OpenDevicePartnership/pico-de-gallo/docs/superpowers/specs/2026-08-19-zephyr-mfd-m5-acceptance.md

# Zephyr MFD restructure M5 — loopback integration and hardware acceptance

Date: 2026-08-19
Branch: `zephyr`, baseline `cfb7f4245ed3`
Milestone: M5 — runtime verification after standard `cs-gpios`
Related implementation: `0affe9206553`
Status: amended after architecture and reliability review

---

## 1. Context, scope and stop conditions

M1–M4 established the MFD topology, GPIO child and standard SPI `cs-gpios`, but
runtime behaviour remains largely unproved. M5 must independently establish:

1. the physical fixture is valid;
2. chip select asserts, holds and releases through GPIO 2↔3;
3. synchronous SPI data is bit-exact on the MOSI↔MISO short;
4. the sanctioned payload ceiling fails locally rather than at transport; and
5. the checked-deassert failure and process-local latch behave as specified.

The fixture is board `5256657D8A5D7F03`, hardware revision 2, attached to WSL by
usbipd. Windows cannot access it while attached. Every build and run is inside
WSL. One process may own USB and one build may run at a time.

### 1.1 Hard boundaries

- Nothing under `crates/`; no wire, firmware, version or lockfile change.
- No firmware flashing, `probe-rs`, GPIO interrupts, or `gallo_*` MCP call.
- No production-driver edit except `PDG_SPI_MAX_BUFFER` and its adjacent comment.
- Test applications may call existing C FFI entry points directly. They may not
  add, alter or emulate an FFI entry point.
- Any other driver defect is stop-and-report, never a silent repair or weakened
  expectation.
- Every hardware process is wall-clock bounded. Timeout is **infrastructure
  failure**, never a test result.
- Any abnormal hardware phase restarts through §9.4. Later phases never consume
  residue from an abnormal predecessor.

---

## 2. Architecture and complete file set

Normal acceptance is serialized:

```text
reset_subscriptions -> jumper_preflight -> acceptance -> spi_loopback -> recovery_teardown
```

The images share only the parent-identity DTS fragment. Their topology overlays
are deliberately different. A phase advances only after zero exit, its exact
success marker, and verified USB release.

### 2.1 Authorized M5 files

| Action | Path | Responsibility |
| --- | --- | --- |
| Create | `docs/superpowers/specs/2026-08-19-zephyr-mfd-m5-acceptance.md` | This specification. |
| Create | `zephyr/tests/pdg_mfd_m5/fixture-identity.dtsi` | Explicit lab-fixture serial only. |
| Create | `zephyr/tests/pdg_mfd_m5/common/m5_bottom.{h,c}` | Host-context shim: `reset_subscriptions`, `gpio_subscribe`, `gpio_unsubscribe`, `spi_get_config`. |
| Create | `zephyr/tests/pdg_mfd_m5/reset_subscriptions/{CMakeLists.txt,prj.conf,reset.overlay,src/main.c}` | Parent-only reset image. |
| Create | `zephyr/tests/pdg_mfd_m5/jumper_preflight/{CMakeLists.txt,prj.conf,jumper.overlay,src/main.c}` | Parent+GPIO image; SPI disabled. |
| Create | `zephyr/tests/pdg_mfd_m5/acceptance/{CMakeLists.txt,prj.conf,acceptance.overlay,src/main.c}` | Parent+GPIO+SPI behavioural acceptance, including a payload-before-only execution mode. |
| Create | `zephyr/tests/pdg_mfd_m5/recovery_teardown/{CMakeLists.txt,prj.conf,recovery.overlay,src/main.c}` | Parent+GPIO+SPI recovery and final-state report. |
| Create | `zephyr/tests/pdg_mfd_m5/run-m5.sh` | Serialized probes, bounded runners, restart handling and aggregate verdict. |
| Create | `zephyr/tests/pdg_mfd_m5/spi_loopback.overlay` | Upstream slow/fast children and CS 2. |
| Create | `zephyr/tests/pdg_mfd_m5/spi_loopback.conf` | Async off, 512-byte large buffer, measured latency scale. |
| Modify | `zephyr/drivers/spi/pdg_spi.c` | Constant and adjacent comment only. |
| Modify | `zephyr/drivers/spi/Kconfig` | Keep the additive heap default at 8192; correct the help text to the final ceiling plus allocator metadata/alignment margin. |
| Modify | `zephyr/dts/bindings/spi/odp,pico-de-gallo-spi.yaml` | Both SPI ceiling statements. |
| Modify | `zephyr/README.md` | SPI ceiling row at current line 582. |
| Modify | `book/src/interfaces/spi.md` | Zephyr SPI error ceiling at current lines 212–214. |
| Modify | `zephyr/CHANGELOG.md` | Corrected ceiling and M5 acceptance evidence. |

Grep found other `4096` references in `book/`, but they describe the FFI,
batching, firmware buffers, or generic firmware APIs and remain valid. The I2C
constant and `zephyr/README.md:564` are also unchanged. Same-change parity for
the six Zephyr SPI files above is mandatory; M6 deferral is prohibited.

**Amendment (coordinator, during implementation): `common/m5_bottom.{h,c}`.**
`native_sim` splits into an embedded context (the applications' `src/main.c`) and
a host context (the native simulator runner). `pico_de_gallo.h` is on the host
include path only — `zephyr/CMakeLists.txt` adds it through
`target_compile_options(native_simulator INTERFACE "-I…")` — which is precisely
why every production driver has a `pdg_*_bottom.c`. An embedded translation unit
therefore cannot call `gallo_*` directly, so §1.1's "test applications may call
existing C FFI entry points directly" is unimplementable as written for the four
entry points that have no production bottom half: `gallo_system_reset_subscriptions`
(§3, §10 step 1), `gallo_gpio_subscribe` and `gallo_gpio_unsubscribe` (§6.2 steps
2, 5 and 9), and `gallo_spi_get_config` (§10 step 4). `gallo_gpio_set_config`
(§6.2 step 6) is unaffected: `pdg_gpio_bottom_set_config()` already exposes it.
The shim is wired per-application with `target_sources(native_simulator INTERFACE
…)`, the same mechanism `zephyr/drivers/CMakeLists.txt` already uses; it adds no
FFI entry point, alters none, emulates none, and modifies no production driver.

**Amendment (coordinator): tester escalation E2 needs no value change.**
`CONFIG_HEAP_MEM_POOL_ADD_SIZE_PDG_SPI` in `zephyr/drivers/spi/Kconfig` already
defaults to **8192**, not the 6144 E2 assumed; E2 read the upstream test's
default rather than this module's. The driver's two `k_malloc`s (`pdg_spi.c:457`,
`:464`) leave roughly 1.9 KiB for `sys_heap` metadata, the heap header and
alignment. Only the Kconfig **help text** is wrong — it still says "4096" and
"about 8 KiB" — and that is a §4 documentation-parity fix, not a configuration
change. Do not "fix" the value a second time.

### 2.2 Topology contracts

- **Reset:** parent `okay`; GPIO and SPI explicitly `disabled`.
- **Jumper:** parent and GPIO `okay`; SPI explicitly `disabled`.
- **Acceptance/recovery:** parent, GPIO and SPI `okay`; CS index 2.
- **Loopback:** same controllers plus `slow@0` and `fast@0` at selector 0.

Each build must assert generated devicetree status, not infer topology from
translation units. In particular, reset must prove both children disabled before
its executable may run.

### 2.3 Fixture identity policy

Commit serial `5256657D8A5D7F03`. It is lab-fixture metadata, not a credential.
Because `zephyr/module.yml:11-12` exports `zephyr/tests`, it **ships in clones and
source archives**. It is intentionally excluded only from portable samples,
which retain `REPLACE_WITH_YOUR_PICO_DE_GALLO_SERIAL`. The identity fragment must
say in a comment: “M5 lab fixture only; do not copy this serial into user
overlays.”

### 2.4 No interrupt witness

Do not set `cs-loopback-gpios`. Current upstream `spi.c:140` guards the complete
witness implementation; omission selects no-op helpers at 242–246. Defining it
reaches interrupt configuration at 233 and callback registration at 240. No other
file under the suite's `src/` uses GPIO interrupts.

---

## 3. Reset sequencing and endpoint limits

The reset image is the resolution of the init-order conflict. Parent init performs
strict open before `main()` directly calls
`gallo_system_reset_subscriptions(ctx, &count)`. GPIO/SPI are absent, so monitored
pin 2 cannot fail SPI init first.

Required reset behaviour:

1. require parent readiness and a non-NULL borrowed context;
2. call reset exactly once and compare its return against the symbolic success
   enumerator from the **actual generated cbindgen header**;
3. print reset count and `M5_RESET_PASS` only after success;
4. any failed check terminates nonzero.

Do not write `Status_Ok`, `GalloStatus_Ok`, bare `0`, or another guessed spelling
in the specification-derived implementation. Inspect the generated header during
the build and use its symbolic enumerator. Current cbindgen configuration keeps
`Status` variants unprefixed and `common.c:19` uses `Ok`, but the generated header
is authoritative.

“Idempotent” is conditional: reset is safe when the firmware dispatcher can
service the endpoint. It cannot preempt an outstanding serial, zero-timeout
`gpio/wait-*`; such a wait wedges dispatch device-wide. Reset affects
**subscriptions only**. It does not reset pin modes, pulls, output levels, SPI
configuration, or a Zephyr process's lock/latch state.

Rejected alternatives remain: choosing pin 3 evades cleanup; a parent/GPIO/SPI
hook hides a destructive global mutation; ztest setup runs after SPI init; power
cycle does not exercise the required endpoint.

---
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
