OpenDevicePartnership/pico-de-gallo/docs/superpowers/specs/2026-08-24-zephyr-mfd-m6-docs.md

# Zephyr MFD restructure M6 — documentation consolidation specification

Date: 2026-08-24
Branch baseline: `zephyr` at `80b9139134e8`
Milestone: M6 — reconcile the SP1 record and consolidate user documentation
Status: ready for documentation implementation

---

## 1. Context and authoritative ruling

M1–M5 shipped the MFD parent, nested I2C/SPI children, the GPIO controller,
standard `cs-gpios`, checked chip-select handling, HOLD/LOCK support, and the M5
hardware suite. M6 changes documentation only. It must preserve the dated M1–M5
record while making its early summaries point at the later corrections.

### 1.1 Transfer-ceiling contradiction — ruling

The M5 acceptance artifact is authoritative. At the start of M6, its 512-byte
duplex success evidence disagrees with the comments under
`PDG_SPI_MAX_BUFFER` and the SPI book chapter, both of which incorrectly say no
duplex length was measured working. M6 must bring the source comment, Zephyr
CHANGELOG, SPI binding/Kconfig, README, and book into agreement with this
contract:

- `1013` is the largest **TX-only** length observed to work, twice.
- the exact TX-only boundary is unresolved between 1013 and 1015; 1014 was not
  probed and 1015 hangs;
- full duplex is known to work at 512 and fail at 3072, but its ceiling was not
  measured and duplex at 1013 is unverified;
- `1013` is a local containment limit, not a derived protocol limit or a fix.

Plan §12.1, beginning “Every estimate”, is the loose account. Its statement that a binary sweep
measured the “true ceiling” at approximately 1013 must be superseded. No M6 text
may call 1013 a measured duplex ceiling, a true boundary, or generally usable
payload. This same claim must appear in the plan correction, AGENTS regression
row, Zephyr CHANGELOG, binding, README, and book.

## 2. Scope and prohibitions

Authorized edits are documentation only:

- `docs/superpowers/plans/2026-08-17-zephyr-mfd-restructure.md`
- this specification
- `AGENTS.md`
- `zephyr/CHANGELOG.md`
- `zephyr/README.md`
- `book/src/**`
- `zephyr/dts/bindings/**/*.yaml`, restricted to `description:` prose
- `zephyr/drivers/**/Kconfig`, restricted to `help` prose
- the `PDG_SPI_MAX_BUFFER` comment block in `zephyr/drivers/spi/pdg_spi.c`

Hard prohibitions:

- **No code changes.** Correct a doc when code is authoritative. If a doc is
  right and code is wrong, escalate to the maintainer; do not fix code.
- Nothing under `crates/`; no package version or `Cargo.lock` change.
- Do not touch hardware: no `gallo_*` MCP tool, `probe-rs`, built binary, M5
  acceptance run, or `--ceiling-sweep`.
- No tree-wide checkout/restore/reset/clean, rebase, unrelated amend, repo-wide
  format, push, or force-push.
- Do not edit ignored `book/book/`; `book/.gitignore:1` confirms it is output.
- Normalize every edited text file to LF with `dos2unix`.

`git diff --stat e7087bdc4eee~1..HEAD -- crates/` produced no output. Therefore
SP1 changed no crate and no per-crate CHANGELOG needs an entry. M6 must not
propose one.

## 3. Plan reconciliation

Preserve §§8–12 verbatim in substance. Use additive forward pointers matching
§4's existing “Corrected after M1” precedent.
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
