OpenDevicePartnership/pico-de-gallo/docs/superpowers/specs/2026-07-29-gallo-mcp-per-call-serial-design.md

# gallo-mcp: per-call serial selection with fail-loud disambiguation

**Date:** 2026-07-29
**Crate:** `gallo-mcp` (`crates/pico-de-gallo-mcp`)
**Issue:** [#89](https://github.com/OpenDevicePartnership/pico-de-gallo/issues/89)
**Type:** tool-surface change (host-only; no wire-protocol, no firmware, no schema bump)

## Problem

Device selection in `gallo-mcp` is server-scoped and unobservable. `--serial-number`
is fixed at startup; when it is absent, `connect()` falls back to
`PicoDeGallo::try_new()` — "first match" — which with N>1 boards silently picks an
arbitrary one. Nothing in any tool response says which board answered.
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
