OpenDevicePartnership/pico-de-gallo/crates/pico-de-gallo-mcp/CHANGELOG.md

# Changelog

All notable changes to `gallo-mcp` will be documented in this file.

The format is based on [Keep a Changelog](https://keepachangelog.com/en/1.1.0/),
and this project adheres to [Semantic Versioning](https://semver.org/spec/v2.0.0.html).

## [Unreleased]

### Changed

- `uart_set_config` gained optional `data_bits`, `parity`, and `stop_bits`
  arguments. Omitted fields select 8N1, and the tool now returns the applied
  configuration instead of a bare `"ok"`; `uart_get_config` reports the same
  framing fields. Closes #152.

### Added

- `encoding::validate_request_frame_len`, wired into `i2c_batch` and
  `spi_batch` before either connects to a board. Part of #186.

  The library refuses an over-ceiling batch too, but its refusal reaches an
  agent through `map_pdg_err` as `invalid_params("device error: buffer
  exceeds firmware limit")` — wrong twice over here, since the device never
  received the request and the limit is the transport's rather than the
  firmware buffer's. The local refusal names the encoded size, the limit,
  the overshoot and the remedy.

### Changed

- `spi_batch` now builds its borrowed operations before connecting, so the
  request-frame bound costs no device access. The documented step order was
  updated to match. Part of #186.

- The "deliberately NOT size-checked" comments on both batch tools, which
  cited #158's scope, now describe what actually bounds a batch write: the
  aggregate request frame, not `MAX_TRANSFER_SIZE`. Part of #186.

### Added

- `encoding.rs` now provides `validate_read_count`, `validate_response_len`,
  and `validate_write_payload`, wired into every I²C, SPI, UART, and 1-Wire
  tool that accepts a count or payload, including aggregate batch lengths.
  Part of #158.

  The checks are local rather than merely inherited from the library. A
  library refusal reached an agent through `map_pdg_err`'s `Endpoint` arm as
  `invalid_params("device error: buffer exceeds firmware limit")`: that calls
  a purely local refusal a device error, names no size, and leaves an LLM
  agent guessing what value would work. The new messages name the offending
  size, the applicable limit, and the remedy.

  Size validation deliberately runs before `connect`. Connecting calls
  `system_reset_subscriptions`, which tears down GPIO subscriptions owned by
  other host processes, so an oversized argument must not cause that
  cross-process side effect. This preserves the ordering established for
  issue #104.

### Fixed

- Tool calls can no longer hang forever when the device does not answer; they
  return a timeout error instead. Refs #178.

  Reported as an internal error rather than invalid-params: the request was
  well formed, so telling an agent its arguments were wrong would send it
  rewriting a perfectly good call. The `spi_batch` message additionally
  states that the batch may or may not have executed, so an agent does not
  retry blindly and repeat its writes.
## [0.4.0] — 2026-09-01

### Added

- `status` now always serializes a `build_id` key (`null` until a board is
  reached), and successful connections log the serial, firmware version, and
  build identity at `info` level. The default filter now enables that event;
  `device_info` also carries the new wire field. Closes #159.

## [0.3.0] — 2026-08-27

### Added

- Support for the MCP **2026-07-28** protocol revision, via `rmcp` 3.1.4. A
  session that negotiates it now receives the SEP-2322 `resultType`
  discriminator and the SEP-2549 `ttlMs`/`cacheScope` cache hints on results,
  and the server answers the new stateless `server/discover` RPC. Sessions on
  2025-11-25 and older keep their existing wire shape byte for byte.

  This closes a gap rather than opening one. `rmcp` 2.2.0 already listed
  `2026-07-28` in `ProtocolVersion::KNOWN_VERSIONS` and its
  `negotiate_protocol_version` echoed any known version, so `gallo-mcp`
  already answered `"protocolVersion": "2026-07-28"` to a client that asked
  for it — while implementing none of that revision's semantics
  (`result_type`, `ttl_ms` and `cache_scope` appear nowhere in the 2.2.0
  source, and `server/discover` did not exist). The advertised revision is
  now one the server actually serves.

### Changed

- `spi_batch` validates `cs` against retained, already-validated
  `DeviceInfo::num_gpios` before it transmits, and reports invalid
  parameters distinctly. Payload parsing deliberately precedes `connect()`:
  connecting calls `system_reset_subscriptions()`, which tears down every
  GPIO subscription on the board, including subscriptions owned by other
  processes, so malformed hex cannot cause that destructive cross-process
  side effect. Closes #104.

- The `i2c_write` and `i2c_batch` tools reject an empty write payload with an
  invalid-argument error before connecting to a board, naming the offending
  operation index in the batch case. Previously the empty payload was
  forwarded and surfaced as a device error, which misattributed a bad
  argument to the hardware. `parse_bytes` is deliberately unchanged and still
  maps `""` to an empty vector, because `i2c_write_read` legitimately accepts
  an empty write phase. Closes #136.

- Bumped `rmcp` from 2.2.0 to 3.1.4. The tool surface is unchanged: all 43
  tools, their names, arguments, annotations and JSON payloads are identical,
  and no handler needed editing. The 3.0 breaking change with the widest
  blast radius — MRTR-aware handler return types — is absorbed by
  `#[tool_handler]`, because this crate implements only `get_info` by hand
  and never matches on `ServerResult`. The `server`, `macros`,
  `transport-io` and `schemars` features all still exist and mean the same
  thing; `server` additionally implies `schemars` and `uuid` in 3.x. Closes
  #138.

- Documented that the `i2c_batch` tool executes one I²C transaction: adjacent
  same-direction operations concatenate, direction changes use a repeated
  START, and only the final operation receives a STOP. A bus failure reports
  `failed_op = 0` for the transaction as a whole; validation failures retain an
  exact index. The MCP tool schema is unchanged. Closes #128.

### Fixed

- The server now identifies itself as `gallo-mcp` with this crate's version in
  the `serverInfo` of an `initialize` result, instead of reporting the SDK.
  `get_info` used rmcp's default `Implementation::from_build_env()`, which
  expands `env!("CARGO_CRATE_NAME")` inside rmcp, so clients displayed and
  logged `rmcp 2.2.0` — and would have silently started showing `rmcp 3.1.4`
  after the bump above. The version is read from `CARGO_PKG_VERSION` so a
  release bump cannot leave it stale.

## [0.2.0] — 2026-08-05

### Added

- Optional `serial_number` argument on every tool except `list_devices`, so a
  single server instance can address any attached board per call.
- Calls naming different boards run concurrently. The connection lock is keyed
  on the board rather than on the server, so a long `gpio_wait_*` holds only
  the board it addressed; calls to the *same* board queue.
- A startup warning when `--serial-number` names a board that is not attached
  while others are. A mistyped pin previously started a healthy-looking server
  that then failed every device call for the whole session. It stays a warning,
  not a startup error: running with no board attached and plugging one in
  mid-session is supported. Emitted by default on stderr, so it reaches
  operators whose MCP client sets no `RUST_LOG`; `RUST_LOG` still overrides
  verbosity when set.

### Changed

- **Breaking (tool surface).** Omitting `serial_number` with two or more
  boards attached is now an error listing the available serials, instead of
  silently binding to whichever board enumerated first. The single-board case
  is unchanged: `serial_number` stays optional.
- **Breaking (response shape).** Device tool responses are now wrapped as
  `{ "serial_number": ..., "result": ... }`, reporting which board served the
  call. `list_devices` and `status` are the exceptions: the first opens no
  board, and the second already carries a `serial_number` of its own.
- **Breaking (response shape).** `list_devices` returns an object instead of a
  bare array. Entries gained `pinned` and `default_target` flags, and the
  object adds `pinned`, `serial_number_required`, and a `note` that is present
  only when a serial is required.
- `--serial-number` now pins the server: a tool call naming a different board
  is refused, and `serial_number` stays optional however many boards are
  attached.
- Two or more attached boards reporting the *same* serial number are now
  refused rather than resolved to whichever enumerated first — naming that
  serial no longer identifies a board. This affects one bench configuration:
  the firmware falls back to an all-zero serial when the OTP chip-ID read
  fails, so two such boards collide, and `--serial-number` does not rescue it
  because the pinned path refuses too. Detach all but one.
- Opening a board still resets **every** GPIO subscription on it, including
  ones owned by other host processes. Per-call selection widens which board
  that reaches: previously only the board the server was bound to, now any
  attached board named by any call — including from the `readOnlyHint` tools
  (`status`, `device_info`, `version`, `ping`, `i2c_scan`). `list_devices`
  opens no board and is unaffected.
- `status` no longer reports `attached: false` when selection fails. It never
  errors, and gained `serial_number`, `ambiguous`, `available`, `pinned`, and a
  `reason` for an unresolved target, alongside the existing `firmware_version`,
  `schema_major`, and `schema_minor`.

### Fixed

- Errors raised after a board was successfully opened no longer claim no
  device is attached, which sent an agent looking for a missing board instead
  of a board that stopped responding.

## [0.1.0] — 2026-07-28

### Added

- Initial release of `gallo-mcp`: a Model Context Protocol server that exposes
  a Pico de Gallo USB bridge to AI agents over stdio, built on the
  [`rmcp`](https://crates.io/crates/rmcp) SDK and wrapping `pico-de-gallo-lib`.
- One MCP tool per peripheral operation across I²C, SPI, UART, GPIO, PWM, ADC,
  and 1-Wire (38 tools), plus device tools (`list_devices`, `status`,
  `device_info`, `version`, `ping`) — 43 in total.
- Hex-string byte payloads (`"0x00,0x10"` in; `{ "hex", "bytes" }` out).
- Read tools annotated `readOnlyHint`; write/actuation tools annotated
  `destructiveHint`. Write approval is delegated to the MCP client.
- Timeout-bounded GPIO edge waits (non-zero timeout enforced). No infinite
  waits or push subscriptions in this release.
- Per-call device connection: each tool opens the board, runs, and releases it
  when the call completes, so the board stays free for the `gallo` CLI and
  other host processes between calls. The server starts with no board attached
  and each tool begins working as soon as one is present.
