OpenDevicePartnership/pico-de-gallo/crates/pico-de-gallo-internal/src/lib.rs

//! Shared wire-protocol types for the Pico de Gallo USB bridge.
//!
//! This crate defines the [postcard-rpc](https://docs.rs/postcard-rpc) endpoints,
//! request/response types, and shared constants used by both the firmware
//! ([`pico-de-gallo-firmware`]) and the host-side library ([`pico-de-gallo-lib`]).
//!
//! # Wire Compatibility
//!
//! All types are serialized with [postcard](https://docs.rs/postcard). Postcard
//! encodes enum variants by **index** (0, 1, 2, …), not by discriminant value.
//! Reordering variants in any `enum` in this crate is a **breaking wire change**
//! that will silently corrupt communication between mismatched firmware and host
//! versions.
//!
//! # Feature Flags
//!
//! - **`use-std`** — Enables `Vec<u8>` response types for the host side. Without
//!   this feature (the default for firmware), responses use borrowed `&[u8]` slices.
//!
//! # Crate Organization
//!
//! - **Constants**: [`MICROSOFT_VID`], [`PICO_DE_GALLO_PID`], [`MAX_TRANSFER_SIZE`],
//!   [`MAX_RESPONSE_PAYLOAD`]
//! - **Endpoints**: Defined via the [`postcard_rpc::endpoints!`] macro — see
//!   [`ENDPOINT_LIST`] for the full table.
//! - **I2C types**: [`I2cReadRequest`], [`I2cWriteRequest`], [`I2cWriteReadRequest`],
//!   [`I2cScanRequest`], and their shared error type [`I2cError`].
//! - **SPI types**: [`SpiReadRequest`], [`SpiWriteRequest`], [`SpiTransferRequest`]
//!   and their shared error type [`SpiError`].
//! - **GPIO types**: [`GpioGetRequest`], [`GpioPutRequest`], [`GpioWaitRequest`],
//!   [`GpioState`], [`GpioDirection`], [`GpioPull`], [`GpioSetConfigurationRequest`],
//!   and their shared error type [`GpioError`].
//! - **UART types**: [`UartReadRequest`], [`UartWriteRequest`],
//!   [`UartSetConfigurationRequest`], [`UartConfigurationInfo`],
//!   [`UartDataBits`], [`UartParity`], [`UartStopBits`],
//!   and their shared error type [`UartError`].
//! - **PWM types**: [`PwmSetDutyCycleRequest`], [`PwmGetDutyCycleRequest`],
//!   [`PwmEnableRequest`], [`PwmDisableRequest`], [`PwmSetConfigurationRequest`],
//!   [`PwmGetConfigurationRequest`], [`PwmDutyCycleInfo`], [`PwmConfigurationInfo`],
//!   and their shared error type [`PwmError`].
//! - **ADC types**: [`AdcReadRequest`], [`AdcChannel`], [`AdcConfigurationInfo`],
//!   and their shared error type [`AdcError`].
//! - **1-Wire types**: [`OneWireReadRequest`], [`OneWireWriteRequest`],
//!   [`OneWireWritePullupRequest`], and their shared error type [`OneWireError`].
//! - **Batch types**: [`I2cBatchRequest`], [`I2cBatchError`], [`I2cBatchOp`],
//!   [`SpiBatchRequest`], [`SpiBatchError`], [`SpiBatchOp`], encoding helpers
//!   [`encode_i2c_batch_ops`], [`encode_spi_batch_ops`], and response-length
//!   helpers [`i2c_batch_response_len`], [`spi_batch_response_len`].
//! - **Configuration**: [`I2cSetConfigurationRequest`], [`SpiSetConfigurationRequest`],
//!   [`GpioSetConfigurationRequest`], [`UartSetConfigurationRequest`],
//!   [`PwmSetConfigurationRequest`],
//!   [`I2cFrequency`], [`SpiPhase`], [`SpiPolarity`],
//!   [`GpioDirection`], [`GpioPull`], [`SpiConfigurationInfo`],
//!   [`UartConfigurationInfo`], [`UartDataBits`], [`UartParity`],
//!   [`UartStopBits`].
//! - **Version**: [`VersionInfo`].
//! - **Device Info**: [`DeviceInfo`], [`Capabilities`].

#![cfg_attr(not(feature = "use-std"), no_std)]

use postcard_rpc::{TopicDirection, endpoints, topics};
use postcard_schema::Schema;
use serde::{Deserialize, Serialize};

// Auto-generated schema version constants from Cargo.toml
include!(concat!(env!("OUT_DIR"), "/schema_version.rs"));

/// USB Vendor ID (Microsoft Corporation).
pub const MICROSOFT_VID: u16 = 0x045e;

/// USB Product ID assigned to Pico de Gallo.
pub const PICO_DE_GALLO_PID: u16 = 0x067d;

/// Maximum number of bytes the firmware can handle in a single I2C or SPI
/// transaction. Requests exceeding this limit will be rejected by the
/// firmware with an error.
///
/// This bounds a *request* argument and the firmware's scratch buffer. It
/// is **not** the bound on how much data can come back: see
/// [`MAX_RESPONSE_PAYLOAD`], which is far tighter.
pub const MAX_TRANSFER_SIZE: usize = 4096;

/// The size of the buffer every inbound USB transfer is read into on the
/// host, in bytes.
///
/// `postcard-rpc-0.12.1/src/host_client/raw_nusb.rs:20`:
///
/// ```text
/// // TODO: These should all be configurable, PRs welcome
/// /// The size in bytes of the largest possible IN transfer
/// pub(crate) const MAX_TRANSFER_SIZE: usize = 1024;
/// ```
///
/// Private and non-configurable upstream, hence the copy. A response frame
/// longer than this fills the buffer, the transfer completes, and the
/// remaining bytes land in the *next* transfer as an unparseable fragment.
const HOST_IN_TRANSFER_BUDGET: usize = 1024;

/// Encoded length of the postcard-rpc header on a response frame, in bytes.
///
/// One discriminant byte (`0bNNMM_VVVV`), then a two-byte key, then a
/// four-byte sequence number:
///
/// * **Key — 2 bytes.** The server shrinks every reply key to
///   `Dispatch::min_key_len()`, which `define_dispatch!` derives from
///   `postcard_rpc::server::min_key_needed` over [`ENDPOINT_LIST`],
///   [`TOPICS_IN_LIST`] and [`TOPICS_OUT_LIST`]. For this protocol that is
///   `VarKeyKind::Key2`, pinned by `reply_key_length_is_two_bytes`.
/// * **Sequence number — 4 bytes.** `HostClient::send_resp` builds every
///   request with `VarSeq::Seq4` and the server echoes the request's
///   `seq_no` verbatim. The `VarSeqKind` handed to `try_new_raw_nusb` never
///   takes effect: `VarSeq::resize` is defined in postcard-rpc 0.12.1 and
///   called nowhere in it. Passing `Seq2` therefore buys no header bytes,
///   which is why a hand-rolled `Seq2` probe measures a 5-byte header while
///   the real client gets 7.
const RESPONSE_HEADER_LEN: usize = 1 + 2 + 4;

/// The postcard variant index of a `Result`, in bytes.
///
/// Every response-bearing endpoint answers with `Result<_, E>`, whose `Ok`
/// arm costs one leading byte before the payload.
const RESPONSE_RESULT_TAG_LEN: usize = 1;

/// The postcard varint length prefix on the returned byte sequence, in
/// bytes.
///
/// Two bytes for any length in `128..=16383`, which
/// [`MAX_RESPONSE_PAYLOAD`] is — asserted by
/// `max_response_payload_needs_a_two_byte_length_prefix`.
const RESPONSE_LEN_PREFIX_LEN: usize = 2;

/// Largest byte payload a single response frame can actually deliver to the
/// host.
///
/// This is a *deliverable-response* ceiling, not a firmware buffer bound.
/// The firmware can produce up to [`MAX_TRANSFER_SIZE`] bytes and drive the
/// bus to obtain them, but a response frame larger than the host
/// transport's inbound buffer is truncated in transit and the caller sees a
/// `Postcard(DeserializeUnexpectedEnd)` that looks like a comms fault.
/// Everything the request already did to the bus has still happened.
///
/// # Derivation
///
/// Every byte is accounted for. Nothing here is fitted to the measurement.
///
/// | Bytes | Term |
/// |------:|------|
/// | `1024` | [`HOST_IN_TRANSFER_BUDGET`] |
/// | `-7` | [`RESPONSE_HEADER_LEN`] — 1 discriminant + 2 key + 4 sequence |
/// | `-1` | [`RESPONSE_RESULT_TAG_LEN`] — the `Result` variant index |
/// | `-2` | [`RESPONSE_LEN_PREFIX_LEN`] — the sequence length varint |
/// | **`= 1014`** | |
///
/// # Measurement
///
/// Confirmed on hardware on two separate boards
/// (`5256657D8A5D7F03` in issue #158, `49742081C885AC69` in issue #179) and
/// across `spi/read`, `spi/transfer`, `i2c/read` and `onewire/read`: `1014`
/// bytes return normally, `1015` fails with
/// `Comms(Postcard(DeserializeUnexpectedEnd))`, and the board stays alive.
/// Reading raw USB transfers off `49742081C885AC69` shows the frame for a
/// 1014-byte `spi/read` is exactly 1024 bytes, and 1015 arrives as
/// `1024 + 1`.
///
/// # When this moves
///
/// The value is a property of the *host* transport, which the firmware
/// cannot observe. It is defined here, rather than host-side only, because
/// the firmware is the only place that can decline to begin irreversible
/// bus side effects for a response it will not be able to deliver — see the
/// batch handlers, and issue #179. It moves if postcard-rpc's inbound
/// transfer size changes, or if this protocol grows enough endpoints to
/// need a four-byte key, in which case it drops to 1012 and
/// `reply_key_length_is_two_bytes` fails first.
pub const MAX_RESPONSE_PAYLOAD: usize = HOST_IN_TRANSFER_BUDGET
    - RESPONSE_HEADER_LEN
    - RESPONSE_RESULT_TAG_LEN
    - RESPONSE_LEN_PREFIX_LEN;

// Compile-time invariants on the derivation above. These are assertions,
// not tests, so drift is a build failure rather than something CI has to
// catch.
const _: () = {
    // `RESPONSE_LEN_PREFIX_LEN` assumes a two-byte postcard varint, which
    // is only right while the ceiling lands in `128..=16383`.
    assert!(MAX_RESPONSE_PAYLOAD >= 128);
    assert!(MAX_RESPONSE_PAYLOAD <= 16383);
    // A response bound, and strictly tighter than the request/buffer bound.
    // Conflating the two is the defect in #179.
    assert!(MAX_RESPONSE_PAYLOAD < MAX_TRANSFER_SIZE);
};

/// Size of each postcard-rpc packet buffer on the firmware, in bytes.
///
/// The firmware's `BufStorage` is
/// `PacketBuffers<{FIRMWARE_PACKET_BUFFER}, {FIRMWARE_PACKET_BUFFER}>`, so
/// this constant *is* the buffer rather than a copy of it and the two
/// cannot drift. Both directions are sized the same; only the receive side
/// enters [`MAX_REQUEST_FRAME`]'s derivation, because the transmit side is
/// bounded far earlier by [`MAX_RESPONSE_PAYLOAD`].
///
/// The `+ 1024` is protocol overhead room around a maximal
/// [`MAX_TRANSFER_SIZE`] argument. It is *not* a second payload allowance:
/// a batch can spend all of it on operation data, which is how issue #186
/// reached the frame ceiling.
pub const FIRMWARE_PACKET_BUFFER: usize = MAX_TRANSFER_SIZE + 1024;

/// The one byte of the firmware's receive buffer that a frame may not use.
///
/// A mechanism, not a safety margin. postcard-rpc's `EUsbWireRx::receive`
/// ends a frame when a **short** USB packet arrives, and loops
/// `while !window.is_empty()`. A frame whose length equals the buffer size
/// fills the window with full 64-byte packets, so the loop runs out of
/// window before it ever sees a short packet, falls into its "ran out of
/// space" branch, reads the transfer-terminating zero-length packet there,
/// and reports `WireRxErrorKind::ReceivedMessageTooLarge`. Frames that are
/// a multiple of 64 but *smaller* than the buffer are unaffected, because
/// window remains and the zero-length packet ends the frame normally.
///
/// Derived by reading `receive()`'s control flow, not by measurement:
/// telling "exact fill refused" apart from "window one byte short" needs a
/// firmware whose receive buffer is not a multiple of 64. Issue #180.
const REQUEST_FRAME_EXACT_FILL_PENALTY: usize = 1;

/// Widest postcard-rpc header a *request* frame can carry, in bytes.
///
/// One discriminant byte, then the key, then the sequence number:
///
/// * **Key — 8 bytes.** Unlike the response header, this is not a constant
///   property of the protocol but of the connection's age.
///   `HostClient` starts at `VarKeyKind::Key8` and adopts the server's
///   narrower `Key2` only after it has **received a reply**
///   (`host_client/mod.rs:202`, `:424`, `:431` are the only sites that
///   touch `kkind`). So a process's first request carries 13 bytes of
///   header and every request after the first reply carries 7.
/// * **Sequence number — 4 bytes.** `VarSeq::Seq4` always, for the reason
///   given on [`RESPONSE_HEADER_LEN`].
///
/// The widest — "cold" — value is the one used to bound a request, because
/// `kkind` is private to postcard-rpc and a caller cannot ask which state
/// its client is in. Bounding against the narrow value would accept a frame
/// that is dropped whenever it happens to be the first one a process sends.
/// The cost is six bytes of headroom on a warm connection, which is the
/// right trade for an answer that does not depend on connection state.
/// Pinned by `request_header_encodes_to_thirteen_bytes`.
const REQUEST_HEADER_LEN_MAX: usize = 1 + 8 + 4;

/// Largest request frame the firmware will accept, in bytes, header
/// included.
///
/// # Derivation
///
/// | Bytes | Term |
/// |------:|------|
/// | `5120` | [`FIRMWARE_PACKET_BUFFER`] |
/// | `-1` | [`REQUEST_FRAME_EXACT_FILL_PENALTY`] |
/// | **`= 5119`** | |
///
/// # Why it needs enforcing
///
/// A frame that does not fit is discarded **silently**. postcard-rpc's
/// server maps `WireRxErrorKind::ReceivedMessageTooLarge` to `continue`, so
/// nothing is sent back and the caller sees only its own timeout. Nothing
/// names the argument at fault and no size is suggested that would work.
/// The firmware cannot help: the request never arrives, so the bound has to
/// be applied host-side, before transmission.
///
/// Since issue #158 every host surface caps a single write argument at
/// [`MAX_TRANSFER_SIZE`], which puts the worst-case frame a little over
/// 4110 bytes — a kilobyte clear of this. Batches were the exception:
/// nothing bounded their aggregate outgoing bytes, so `i2c/batch` and
/// `spi/batch` were the one remaining door from a supported host surface
/// into this ceiling (issue #186).
///
/// # Measurement
///
/// Confirmed on board `49742081C885AC69` (hw-rev2, firmware
/// `firmware-v0.11.0-88-gfcb38de3a1ff`) under Linux/nusb, and previously on
/// the same board under firmware `-79-gc3c6a3e07bec` across sixteen
/// boundaries spanning four key widths (issue #180). Driven through
/// `pico-de-gallo-lib`'s `i2c_batch`, a frame of `5119` bytes is executed
/// and answers; `5120` is dropped and the call times out. The edge sits at
/// the same frame length cold and warm, six payload bytes apart, which is
/// what identifies it as a *frame* ceiling rather than a payload one.
///
/// # When this moves
///
/// It tracks the firmware's receive buffer, which is why that buffer is
/// [`FIRMWARE_PACKET_BUFFER`] rather than a literal. Unlike
/// [`MAX_RESPONSE_PAYLOAD`] this is a property of the *device*, so a host
/// built against a firmware with a different buffer would be wrong — the
/// two travel together in the same release (§6.5).
pub const MAX_REQUEST_FRAME: usize = FIRMWARE_PACKET_BUFFER - REQUEST_FRAME_EXACT_FILL_PENALTY;

// Compile-time invariants on the derivation above, matching the treatment
// `MAX_RESPONSE_PAYLOAD` gets.
const _: () = {
    // The header has to leave room for a payload at all. Anything near this
    // means a term is wrong by orders of magnitude.
    assert!(MAX_REQUEST_FRAME > REQUEST_HEADER_LEN_MAX);
    // The request budget is the looser of the two directions. Every
    // send-direction bound in `pico-de-gallo-lib` relies on this ordering,
    // and #179 is what conflating them looks like.
    assert!(MAX_RESPONSE_PAYLOAD < MAX_REQUEST_FRAME);
    // A single maximal write argument must stay clear of the frame ceiling,
    // or #158's per-argument bounds would themselves be reachable here and
    // every plain endpoint would need this check too.
    assert!(MAX_TRANSFER_SIZE + REQUEST_HEADER_LEN_MAX < MAX_REQUEST_FRAME);
};

/// Ceiling the firmware applies to any caller-supplied handler timeout.
///
/// A `timeout_ms` of `0` does **not** mean "wait forever": both `0` and
/// oversized values clamp to this, after which the handler returns its normal
/// `Timeout` error. Hosts use this to bound how long a call carrying a
/// caller-supplied duration can legitimately take.
///
/// Mirrored by `MAX_HANDLER_TIMEOUT` in the firmware's `progress` module,
/// which derives its `Duration` from this constant so the two cannot drift.
pub const MAX_HANDLER_TIMEOUT_MS: u32 = 30 * 60 * 1000;

/// Supervisor budget the firmware grants a handler that declares no budget of
/// its own.
///
/// Sized to cover `i2c/scan`'s worst case (128 addresses × 50 ms = 6.4 s) with
/// margin. Hosts use this to bound calls that are slow but carry no
/// caller-supplied duration — `i2c/scan` above all, which legitimately exceeds
/// a typical per-call default.
///
/// Mirrored by `DEFAULT_DISPATCH_BUDGET` in the firmware's `progress` module,
/// which derives its `Duration` from this constant so the two cannot drift.
pub const UNDECLARED_DISPATCH_BUDGET_MS: u32 = 10_000;

// ---

/// Response type for I2C write operations.
pub type I2cWriteResponse = Result<(), I2cError>;

/// Response type for I2C read operations.
/// On the host (`use-std`), returns `Vec<u8>`; on firmware, returns `&[u8]`.
#[cfg(feature = "use-std")]
pub type I2cReadResponse<'a> = Result<Vec<u8>, I2cError>;
/// Response type for I2C read operations.
/// On the host (`use-std`), returns `Vec<u8>`; on firmware, returns `&[u8]`.
#[cfg(not(feature = "use-std"))]
pub type I2cReadResponse<'a> = Result<&'a [u8], I2cError>;

/// Response type for I2C write-read operations.
/// On the host (`use-std`), returns `Vec<u8>`; on firmware, returns `&[u8]`.
#[cfg(feature = "use-std")]
pub type I2cWriteReadResponse<'a> = Result<Vec<u8>, I2cError>;
/// Response type for I2C write-read operations.
/// On the host (`use-std`), returns `Vec<u8>`; on firmware, returns `&[u8]`.
#[cfg(not(feature = "use-std"))]
pub type I2cWriteReadResponse<'a> = Result<&'a [u8], I2cError>;

/// Response type for SPI write operations.
pub type SpiWriteResponse = Result<(), SpiError>;

/// Response type for SPI read operations.
/// On the host (`use-std`), returns `Vec<u8>`; on firmware, returns `&[u8]`.
#[cfg(feature = "use-std")]
pub type SpiReadResponse<'a> = Result<Vec<u8>, SpiError>;
/// Response type for SPI read operations.
/// On the host (`use-std`), returns `Vec<u8>`; on firmware, returns `&[u8]`.
#[cfg(not(feature = "use-std"))]
pub type SpiReadResponse<'a> = Result<&'a [u8], SpiError>;

/// Response type for SPI flush operations.
pub type SpiFlushResponse = Result<(), SpiError>;

/// Response type for SPI transfer operations.
/// On the host (`use-std`), returns `Vec<u8>`; on firmware, returns `&[u8]`.
#[cfg(feature = "use-std")]
pub type SpiTransferResponse<'a> = Result<Vec<u8>, SpiError>;
/// Response type for SPI transfer operations.
/// On the host (`use-std`), returns `Vec<u8>`; on firmware, returns `&[u8]`.
#[cfg(not(feature = "use-std"))]
pub type SpiTransferResponse<'a> = Result<&'a [u8], SpiError>;

/// Response type for GPIO get operations.
pub type GpioGetResponse = Result<GpioState, GpioError>;
/// Response type for GPIO put operations.
pub type GpioPutResponse = Result<(), GpioError>;
/// Response type for GPIO wait operations.
pub type GpioWaitResponse = Result<(), GpioError>;
/// Response type for GPIO set-configuration operations.
pub type GpioSetConfigurationResponse = Result<(), GpioError>;
/// Response type for GPIO subscribe operations.
pub type GpioSubscribeResponse = Result<(), GpioError>;
/// Response type for GPIO unsubscribe operations.
pub type GpioUnsubscribeResponse = Result<(), GpioError>;
/// Response type for `system/reset-subscriptions`.
///
/// Returns the number of GPIO subscriptions that were torn down (0 if
/// none were active). Always succeeds — the endpoint is idempotent and
/// is meant to be called by hosts on connect to clean up any
/// subscriptions that survived a previous host crash, disconnect, or
/// `nusb::Interface` drop.
pub type SystemResetSubscriptionsResponse = u8;
/// Response type for I2C bus configuration operations.
pub type I2cSetConfigurationResponse = Result<(), I2cConfigError>;
/// Response type for I2C bus scan operations.
/// On the host (`use-std`), returns `Vec<u8>` of responding addresses;
/// on firmware, returns `&[u8]`.
#[cfg(feature = "use-std")]
pub type I2cScanResponse<'a> = Result<Vec<u8>, I2cError>;
/// Response type for I2C bus scan operations.
/// On the host (`use-std`), returns `Vec<u8>` of responding addresses;
/// on firmware, returns `&[u8]`.
#[cfg(not(feature = "use-std"))]
pub type I2cScanResponse<'a> = Result<&'a [u8], I2cError>;
/// Response type for SPI bus configuration operations.
pub type SpiSetConfigurationResponse = Result<(), SpiConfigError>;

/// Response type for I2C get-configuration queries.
///
/// Returns the currently active I2C bus frequency.
pub type I2cGetConfigurationResponse = I2cFrequency;

/// Response type for SPI get-configuration queries.
///
/// Returns the currently active SPI bus parameters.
pub type SpiGetConfigurationResponse = SpiConfigurationInfo;

/// Response type for UART write operations.
pub type UartWriteResponse = Result<(), UartError>;

/// Response type for UART read operations.
/// On the host (`use-std`), returns `Vec<u8>`; on firmware, returns `&[u8]`.
#[cfg(feature = "use-std")]
pub type UartReadResponse<'a> = Result<Vec<u8>, UartError>;
/// Response type for UART read operations.
/// On the host (`use-std`), returns `Vec<u8>`; on firmware, returns `&[u8]`.
#[cfg(not(feature = "use-std"))]
pub type UartReadResponse<'a> = Result<&'a [u8], UartError>;

/// Response type for UART flush operations.
pub type UartFlushResponse = Result<(), UartError>;

/// Response type for UART bus configuration operations.
pub type UartSetConfigurationResponse = Result<(), UartConfigError>;

/// Response type for UART get-configuration queries.
///
/// Returns the currently active UART parameters.
pub type UartGetConfigurationResponse = Result<UartConfigurationInfo, UartError>;

/// Response type for PWM set-duty-cycle operations.
pub type PwmSetDutyCycleResponse = Result<(), PwmError>;
/// Response type for PWM get-duty-cycle queries.
pub type PwmGetDutyCycleResponse = Result<PwmDutyCycleInfo, PwmError>;
/// Response type for PWM enable operations.
pub type PwmEnableResponse = Result<(), PwmError>;
/// Response type for PWM disable operations.
pub type PwmDisableResponse = Result<(), PwmError>;
/// Response type for PWM set-configuration operations.
pub type PwmSetConfigurationResponse = Result<(), PwmConfigError>;
/// Response type for PWM get-configuration queries.
pub type PwmGetConfigurationResponse = Result<PwmConfigurationInfo, PwmError>;

/// Response type for ADC read operations.
pub type AdcReadResponse = Result<u16, AdcError>;
/// Response type for ADC get-configuration queries.
pub type AdcGetConfigurationResponse = Result<AdcConfigurationInfo, AdcError>;

/// Response type for 1-Wire reset operations.
/// Returns `true` if at least one device is present on the bus.
pub type OneWireResetResponse = Result<bool, OneWireError>;

/// Response type for 1-Wire read operations.
/// On the host (`use-std`), returns `Vec<u8>`; on firmware, returns `&[u8]`.
#[cfg(feature = "use-std")]
pub type OneWireReadResponse<'a> = Result<Vec<u8>, OneWireError>;
/// Response type for 1-Wire read operations.
/// On the host (`use-std`), returns `Vec<u8>`; on firmware, returns `&[u8]`.
#[cfg(not(feature = "use-std"))]
pub type OneWireReadResponse<'a> = Result<&'a [u8], OneWireError>;

/// Response type for 1-Wire write operations.
pub type OneWireWriteResponse = Result<(), OneWireError>;

/// Response type for 1-Wire write-with-pullup operations.
pub type OneWireWritePullupResponse = Result<(), OneWireError>;

/// Response type for 1-Wire ROM search operations.
/// Returns `Some(rom_id)` for the next device found, or `None` if the
/// search is complete.
pub type OneWireSearchResponse = Result<Option<u64>, OneWireError>;

/// Response type for I2C batch transaction operations.
/// On the host (`use-std`), returns `Vec<u8>` of concatenated read data;
/// on firmware, returns `&[u8]`.
#[cfg(feature = "use-std")]
pub type I2cBatchResponse<'a> = Result<Vec<u8>, I2cBatchError>;
/// Response type for I2C batch transaction operations.
/// On the host (`use-std`), returns `Vec<u8>` of concatenated read data;
/// on firmware, returns `&[u8]`.
#[cfg(not(feature = "use-std"))]
pub type I2cBatchResponse<'a> = Result<&'a [u8], I2cBatchError>;

/// Response type for SPI batch transaction operations.
/// On the host (`use-std`), returns `Vec<u8>` of concatenated read/transfer data;
/// on firmware, returns `&[u8]`.
#[cfg(feature = "use-std")]
pub type SpiBatchResponse<'a> = Result<Vec<u8>, SpiBatchError>;
/// Response type for SPI batch transaction operations.
/// On the host (`use-std`), returns `Vec<u8>` of concatenated read/transfer data;
/// on firmware, returns `&[u8]`.
#[cfg(not(feature = "use-std"))]
pub type SpiBatchResponse<'a> = Result<&'a [u8], SpiBatchError>;

endpoints! {
    list = ENDPOINT_LIST;
    | EndpointTy          | RequestTy                  | ResponseTy                  | Path                |
    | ----------          | ---------                  | ----------                  | ----                |
    | PingEndpoint        | u32                        | u32                         | "ping"              |
    | I2cRead             | I2cReadRequest             | I2cReadResponse<'a>         | "i2c/read"          |
    | I2cWrite            | I2cWriteRequest<'a>        | I2cWriteResponse            | "i2c/write"         |
    | I2cWriteRead        | I2cWriteReadRequest<'a>    | I2cWriteReadResponse<'b>    | "i2c/write-read"    |
    | SpiRead             | SpiReadRequest             | SpiReadResponse<'a>         | "spi/read"          |
    | SpiWrite            | SpiWriteRequest<'a>        | SpiWriteResponse            | "spi/write"         |
    | SpiFlush            | ()                         | SpiFlushResponse            | "spi/flush"         |
    | SpiTransfer         | SpiTransferRequest<'a>     | SpiTransferResponse<'b>     | "spi/transfer"      |
    | GpioGet             | GpioGetRequest             | GpioGetResponse             | "gpio/get"          |
    | GpioPut             | GpioPutRequest             | GpioPutResponse             | "gpio/put"          |
    | GpioWaitForHigh     | GpioWaitRequest            | GpioWaitResponse            | "gpio/wait-high"    |
    | GpioWaitForLow      | GpioWaitRequest            | GpioWaitResponse            | "gpio/wait-low"     |
    | GpioWaitForRising   | GpioWaitRequest            | GpioWaitResponse            | "gpio/wait-rising"  |
    | GpioWaitForFalling  | GpioWaitRequest            | GpioWaitResponse            | "gpio/wait-falling" |
    | GpioWaitForAny      | GpioWaitRequest            | GpioWaitResponse            | "gpio/wait-any"     |
    | I2cSetConfiguration | I2cSetConfigurationRequest | I2cSetConfigurationResponse | "i2c/set-config"    |
    | I2cScan             | I2cScanRequest             | I2cScanResponse<'a>         | "i2c/scan"          |
    | SpiSetConfiguration  | SpiSetConfigurationRequest  | SpiSetConfigurationResponse  | "spi/set-config"    |
    | GpioSetConfiguration | GpioSetConfigurationRequest | GpioSetConfigurationResponse | "gpio/set-config"   |
    | I2cGetConfiguration  | ()                          | I2cGetConfigurationResponse  | "i2c/get-config"    |
    | SpiGetConfiguration  | ()                          | SpiGetConfigurationResponse  | "spi/get-config"    |
    | UartRead             | UartReadRequest             | UartReadResponse<'a>         | "uart/read"         |
    | UartWrite            | UartWriteRequest<'a>        | UartWriteResponse            | "uart/write"        |
    | UartFlush            | ()                          | UartFlushResponse            | "uart/flush"        |
    | UartSetConfiguration | UartSetConfigurationRequest | UartSetConfigurationResponse | "uart/set-config"   |
    | UartGetConfiguration  | ()                            | UartGetConfigurationResponse  | "uart/get-config"    |
    | PwmSetDutyCycle       | PwmSetDutyCycleRequest        | PwmSetDutyCycleResponse       | "pwm/set-duty-cycle" |
    | PwmGetDutyCycle       | PwmGetDutyCycleRequest        | PwmGetDutyCycleResponse       | "pwm/get-duty-cycle" |
    | PwmEnable             | PwmEnableRequest              | PwmEnableResponse             | "pwm/enable"         |
    | PwmDisable            | PwmDisableRequest             | PwmDisableResponse            | "pwm/disable"        |
    | PwmSetConfiguration   | PwmSetConfigurationRequest    | PwmSetConfigurationResponse   | "pwm/set-config"     |
    | PwmGetConfiguration   | PwmGetConfigurationRequest    | PwmGetConfigurationResponse   | "pwm/get-config"     |
    | AdcRead               | AdcReadRequest                | AdcReadResponse               | "adc/read"           |
    | AdcGetConfiguration   | ()                            | AdcGetConfigurationResponse   | "adc/get-config"     |
    | GpioSubscribe         | GpioSubscribeRequest          | GpioSubscribeResponse         | "gpio/subscribe"     |
    | GpioUnsubscribe       | GpioUnsubscribeRequest        | GpioUnsubscribeResponse       | "gpio/unsubscribe"   |
    | I2cBatch              | I2cBatchRequest<'a>           | I2cBatchResponse<'b>          | "i2c/batch"          |
    | SpiBatch              | SpiBatchRequest<'a>           | SpiBatchResponse<'b>          | "spi/batch"          |
    | OneWireReset          | ()                            | OneWireResetResponse          | "onewire/reset"      |
    | OneWireRead           | OneWireReadRequest            | OneWireReadResponse<'a>       | "onewire/read"       |
    | OneWireWrite          | OneWireWriteRequest<'a>       | OneWireWriteResponse          | "onewire/write"      |
    | OneWireWritePullup    | OneWireWritePullupRequest<'a> | OneWireWritePullupResponse    | "onewire/write-pullup" |
    | OneWireSearch         | ()                            | OneWireSearchResponse         | "onewire/search"     |
    | OneWireSearchNext     | ()                            | OneWireSearchResponse         | "onewire/search-next" |
    | Version               | ()                            | VersionInfo                   | "version"            |
    | GetDeviceInfo         | ()                            | DeviceInfo                    | "device/info"        |
    | SystemResetSubscriptions | ()                         | SystemResetSubscriptionsResponse | "system/reset-subscriptions" |
}

topics! {
    list = TOPICS_IN_LIST;
    direction = TopicDirection::ToServer;
    | TopicTy | MessageTy | Path |
    | ------- | --------- | ---- |
}

topics! {
    list = TOPICS_OUT_LIST;
    direction = TopicDirection::ToClient;
    | TopicTy         | MessageTy  | Path              | Cfg |
    | -------         | --------- | ----               | --- |
    | GpioEventTopic    | GpioEvent   | "gpio/event"    |     |
}

// --- I2C

/// Request to write bytes to an I2C device, then read back.
///
/// The firmware performs a write followed by a repeated-start read in a
/// single I2C transaction, which is the standard pattern for reading
/// registers from most I2C devices.
#[derive(Serialize, Deserialize, Schema, Debug, PartialEq)]
pub struct I2cWriteReadRequest<'a> {
    /// 7-bit I2C slave address.
    pub address: u8,
    /// Bytes to write (typically a register address).
    pub contents: &'a [u8],
    /// Number of bytes to read back (max [`MAX_TRANSFER_SIZE`]).
    pub count: u16,
}

/// Error from I2C operations, propagated from firmware.
///
/// Maps directly to [`embedded_hal::i2c::ErrorKind`] variants on the host side.
///
/// # Wire Compatibility
///
/// Variants are serialized by **index** (0, 1, 2, …). Do **not** reorder,
/// rename, or insert variants in the middle — only append new variants at
/// the end. Removing or reordering is a breaking wire change.
#[derive(Serialize, Deserialize, Schema, Debug, Clone, Copy, PartialEq, Eq)]
pub enum I2cError {
    /// Bus error (unexpected condition on the I2C bus).
    Bus,
    /// No acknowledge received from the target device.
    NoAcknowledge,
    /// Arbitration lost to another controller on the bus.
    ArbitrationLoss,
    /// Data overrun — firmware could not keep up with the bus clock.
    Overrun,
    /// A length bound was exceeded.
    ///
    /// One of three bounds was exceeded: a request argument past the
    /// firmware buffer limit ([`MAX_TRANSFER_SIZE`]); a batch whose `Read`
    /// operations would return more than [`MAX_RESPONSE_PAYLOAD`] bytes in
    /// total, more than one response frame can carry (issue #179); or a
    /// batch whose whole request frame would exceed [`MAX_REQUEST_FRAME`]
    /// (issue #186). Nothing on the wire tells them apart, so consult all
    /// three. The last is refused host-side only — the device never
    /// receives such a frame and so can never report it.
    BufferTooLong,
    /// I2C address is outside the valid 7-bit range (0x00–0x7F).
    AddressOutOfRange,
    /// An unspecified error occurred in the firmware.
    Other,
    /// A write was requested with an empty payload.
    ///
    /// The RP2040/RP2350 `DW_apb_i2c` block cannot emit an address-only
    /// transaction: the address phase is driven solely by pushing at least
    /// one byte into `IC_DATA_CMD`, so `START + ADDR + STOP` is physically
    /// unreachable (rp-rs/rp-hal#678, embassy-rs/embassy#4474). Forwarding
    /// such a write to `embassy_rp::i2c::write_async` starts no transaction
    /// yet still waits for a `STOP_DET`/`TX_ABRT` interrupt that can never
    /// arrive, which wedges the firmware dispatcher device-wide. The
    /// firmware therefore refuses the request up front. Probe an address
    /// with a 1-byte read (`i2c/read`) or with `i2c/scan` instead.
    ZeroLengthWrite,
}

impl core::fmt::Display for I2cError {
    fn fmt(&self, f: &mut core::fmt::Formatter<'_>) -> core::fmt::Result {
        match self {
            Self::Bus => write!(f, "I2C bus error"),
            Self::NoAcknowledge => write!(f, "no acknowledge from target"),
            Self::ArbitrationLoss => write!(f, "I2C arbitration loss"),
            Self::Overrun => write!(f, "I2C data overrun"),
            Self::BufferTooLong => write!(f, "buffer exceeds firmware limit"),
            Self::AddressOutOfRange => write!(f, "I2C address out of range"),
            Self::Other => write!(f, "I2C error"),
            Self::ZeroLengthWrite => {
                write!(f, "zero-length I2C write is not supported by this hardware")
            }
        }
    }
}

/// Request to read bytes from an I2C device.
#[derive(Serialize, Deserialize, Schema, Debug, PartialEq)]
pub struct I2cReadRequest {
    /// 7-bit I2C slave address.
    pub address: u8,
    /// Number of bytes to read (max [`MAX_TRANSFER_SIZE`]).
    pub count: u16,
}

/// Request to write bytes to an I2C device.
#[derive(Serialize, Deserialize, Schema, Debug, PartialEq)]
pub struct I2cWriteRequest<'a> {
    /// 7-bit I2C slave address.
    pub address: u8,
    /// Bytes to write.
    pub contents: &'a [u8],
}

/// Request to scan the I2C bus for responding devices.
///
/// The firmware probes addresses by attempting a 1-byte read at each
/// 7-bit address. Addresses that ACK are included in the response.
#[derive(Serialize, Deserialize, Schema, Debug, PartialEq)]
pub struct I2cScanRequest {
    /// When `true`, also probe reserved addresses (0x00–0x07 and 0x78–0x7F).
    /// When `false`, only probe the standard range 0x08–0x77.
    pub include_reserved: bool,
}

// --- SPI

/// Error from SPI operations, propagated from firmware.
///
/// # Wire Compatibility
///
/// Variants are serialized by **index**. Do **not** reorder or insert
/// variants in the middle — only append at the end.
#[derive(Serialize, Deserialize, Schema, Debug, Clone, Copy, PartialEq, Eq)]
pub enum SpiError {
    /// A length bound was exceeded.
    ///
    /// One of three bounds was exceeded: a request argument past the
    /// firmware buffer limit ([`MAX_TRANSFER_SIZE`]); a batch whose `Read`
    /// and `Transfer` operations would return more than
    /// [`MAX_RESPONSE_PAYLOAD`] bytes in total, more than one response
    /// frame can carry (issue #179); or a batch whose whole request frame
    /// would exceed [`MAX_REQUEST_FRAME`] (issue #186). Nothing on the wire
    /// tells them apart, so consult all three. The last is refused
    /// host-side only — the device never receives such a frame and so can
    /// never report it.
    BufferTooLong,
    /// An unspecified error occurred in the firmware.
    Other,
    /// The requested chip-select pin is outside the bound reported by
    /// [`DeviceInfo::num_gpios`].
    InvalidCsPin,
    /// The chip-select pin is explicitly configured as an input; it is left
    /// unchanged.
    CsPinUnavailable,
    /// The chip-select pin is being monitored for GPIO events; it is left
    /// unchanged.
    CsPinMonitored,
}

impl core::fmt::Display for SpiError {
    fn fmt(&self, f: &mut core::fmt::Formatter<'_>) -> core::fmt::Result {
        match self {
            Self::BufferTooLong => write!(f, "buffer exceeds firmware limit"),
            Self::Other => write!(f, "SPI error"),
            Self::InvalidCsPin => write!(f, "invalid SPI chip-select pin"),
            Self::CsPinUnavailable => {
                write!(f, "SPI chip-select pin is configured as input")
            }
            Self::CsPinMonitored => {
                write!(f, "SPI chip-select pin is being monitored for events")
            }
        }
    }
}

/// Request to read bytes from the SPI bus.
#[derive(Serialize, Deserialize, Schema, Debug, PartialEq)]
pub struct SpiReadRequest {
    /// Number of bytes to read (max [`MAX_TRANSFER_SIZE`]).
    pub count: u16,
}

/// Request to write bytes to the SPI bus.
#[derive(Serialize, Deserialize, Schema, Debug, PartialEq)]
pub struct SpiWriteRequest<'a> {
    /// Bytes to write.
    pub contents: &'a [u8],
}

/// Request for a full-duplex SPI transfer.
///
/// The firmware simultaneously transmits `contents` and receives the same
/// number of bytes. This is a true full-duplex operation using DMA.
#[derive(Serialize, Deserialize, Schema, Debug, PartialEq)]
pub struct SpiTransferRequest<'a> {
    /// Bytes to transmit. The response will contain the same number of received bytes.
    pub contents: &'a [u8],
}

/// Error returned when an SPI transfer operation fails.
///
/// This is a convenience alias — SPI transfers share the same error type
/// as other SPI operations.
pub type SpiTransferError = SpiError;

// --- GPIO

/// Compile-time default number of user-controllable GPIO pins.
///
/// Pin indices 0–3 map to physical GPIO8–GPIO11 on the Pico 2 header.
/// Requests naming an index at or above this bound are rejected with
/// [`GpioError::InvalidPin`].
///
/// The same indices double as SPI chip-select selectors: see
/// [`SpiBatchRequest::cs_pin`]. The header pin silkscreened `SPI_CS`
/// (GPIO5) is a PCB net label rather than a usable chip select: it is
/// *not* one of these indices, and no firmware claims or drives it.
/// See [issue #99](https://github.com/OpenDevicePartnership/pico-de-gallo/issues/99).
///
/// Host code must use [`DeviceInfo::num_gpios`] as the runtime-authoritative
/// count. This constant is only the compile-time default.
pub const NUM_GPIOS: usize = 4;

const _: () = assert!(NUM_GPIOS <= u8::MAX as usize);

/// Request to read the current level of a GPIO pin.
#[derive(Serialize, Deserialize, Schema, Debug, PartialEq)]
pub struct GpioGetRequest {
    /// GPIO pin index (0–3).
    pub pin: u8,
}

/// Error from GPIO operations, propagated from firmware.
///
/// # Wire Compatibility
///
/// Variants are serialized by **index**. Do **not** reorder or insert
/// variants in the middle — only append at the end.
#[derive(Serialize, Deserialize, Schema, Debug, Clone, Copy, PartialEq, Eq)]
pub enum GpioError {
    /// The requested pin number is invalid (outside 0–3 range).
    InvalidPin,
    /// An unspecified error occurred in the firmware.
    Other,
    /// The pin is configured in a direction that does not support this operation.
    WrongDirection,
    /// The pin is currently being monitored for events and cannot be used
    /// for regular GPIO operations. Unsubscribe first.
    PinMonitored,
    /// The pin is not currently monitored — cannot unsubscribe.
    PinNotMonitored,
    /// Returned by `gpio_wait_*` endpoints when the host-supplied
    /// `timeout_ms` elapses before the requested edge or level is detected.
    /// Introduced in schema 0.7. A `timeout_ms` of `0` selects the firmware's
    /// 30-minute ceiling; oversized values are clamped to the same ceiling.
    Timeout,
}

impl core::fmt::Display for GpioError {
    fn fmt(&self, f: &mut core::fmt::Formatter<'_>) -> core::fmt::Result {
        match self {
            Self::InvalidPin => write!(f, "invalid GPIO pin number"),
            Self::Other => write!(f, "GPIO error"),
            Self::WrongDirection => write!(f, "GPIO pin configured in wrong direction"),
            Self::PinMonitored => write!(f, "GPIO pin is being monitored for events"),
            Self::PinNotMonitored => write!(f, "GPIO pin is not monitored"),
            Self::Timeout => write!(f, "GPIO wait timed out"),
        }
    }
}

/// Request to set a GPIO pin to a specific level.
#[derive(Serialize, Deserialize, Schema, Debug, PartialEq)]
pub struct GpioPutRequest {
    /// GPIO pin index (0–3).
    pub pin: u8,
    /// Desired output level.
    pub state: GpioState,
}

/// Logic level of a GPIO pin.
//
// WARNING: Do not reorder enum variants — postcard serializes by
// variant index, not by discriminant. Reordering breaks wire compat.
#[derive(Serialize, Deserialize, Schema, Debug, Clone, Copy, PartialEq, Eq, Hash)]
pub enum GpioState {
    /// Logic low (0V).
    Low,
    /// Logic high (3.3V on RP2350).
    High,
}

impl From<bool> for GpioState {
    fn from(value: bool) -> Self {
        if value {
            GpioState::High
        } else {
            GpioState::Low
        }
    }
}

impl From<GpioState> for bool {
    fn from(state: GpioState) -> Self {
        matches!(state, GpioState::High)
    }
}

/// Request to wait for a GPIO pin to reach a specific state or edge.
#[derive(Serialize, Deserialize, Schema, Debug, PartialEq)]
pub struct GpioWaitRequest {
    /// GPIO pin index (0–3).
    pub pin: u8,
    /// Per-request timeout in milliseconds. A value of `0` selects the
    /// firmware's 30-minute ceiling; oversized values are clamped to the same
    /// ceiling. Expiry returns [`GpioError::Timeout`].
    pub timeout_ms: u32,
}

/// GPIO pin direction.
//
// WARNING: Do not reorder enum variants — postcard serializes by
// variant index, not by discriminant. Reordering breaks wire compat.
#[derive(Serialize, Deserialize, Schema, Debug, Clone, Copy, PartialEq, Eq, Hash)]
#[repr(u8)]
pub enum GpioDirection {
    /// Configure the pin as a digital input.
    Input = 0,
    /// Configure the pin as a digital output.
    Output = 1,
}

/// GPIO internal pull resistor configuration.
//
// WARNING: Do not reorder enum variants — postcard serializes by
// variant index, not by discriminant. Reordering breaks wire compat.
#[derive(Serialize, Deserialize, Schema, Debug, Clone, Copy, PartialEq, Eq, Hash)]
#[repr(u8)]
pub enum GpioPull {
    /// No internal pull resistor.
    None = 0,
    /// Internal pull-up resistor enabled.
    Up = 1,
    /// Internal pull-down resistor enabled.
    Down = 2,
}

/// Request to configure a GPIO pin's direction and pull resistor.
///
/// After configuration, the pin retains its explicit mode until the
/// firmware is reset. See [`GpioDirection`] and [`GpioPull`] for
/// available options.
#[derive(Serialize, Deserialize, Schema, Debug, PartialEq)]
pub struct GpioSetConfigurationRequest {
    /// GPIO pin index (0–3).
    pub pin: u8,
    /// Desired pin direction.
    pub direction: GpioDirection,
    /// Internal pull resistor setting.
    pub pull: GpioPull,
}

// --- GPIO event monitoring

/// Edge type for GPIO event monitoring.
///
/// Selects which transitions trigger a [`GpioEvent`] notification.
///
/// # Wire Compatibility
///
/// Variants are serialized by **index**. Do **not** reorder or insert
/// variants in the middle — only append at the end.
#[derive(Serialize, Deserialize, Schema, Debug, Clone, Copy, PartialEq, Eq, Hash)]
#[repr(u8)]
pub enum GpioEdge {
    /// Trigger on low-to-high transitions.
    Rising = 0,
    /// Trigger on high-to-low transitions.
    Falling = 1,
    /// Trigger on any transition (rising or falling).
    Any = 2,
}

impl core::fmt::Display for GpioEdge {
    fn fmt(&self, f: &mut core::fmt::Formatter<'_>) -> core::fmt::Result {
        match self {
            Self::Rising => write!(f, "rising"),
            Self::Falling => write!(f, "falling"),
            Self::Any => write!(f, "any"),
        }
    }
}

/// A GPIO event notification published by the firmware.
///
/// Sent as a [`GpioEventTopic`] message whenever a monitored pin detects
/// an edge matching its subscription. The host receives these via
/// [`postcard_rpc::host_client::HostClient::subscribe`].
///
/// **Note:** Event delivery is best-effort. Edges faster than the
/// firmware's monitor loop may be coalesced or missed.
#[derive(Serialize, Deserialize, Schema, Debug, Clone, PartialEq, Eq)]
pub struct GpioEvent {
    /// GPIO pin index (0–3) that triggered the event.
    pub pin: u8,
    /// The edge type that was detected.
    pub edge: GpioEdge,
    /// Pin level sampled immediately after the event (may differ from
    /// the triggering edge if the signal bounced).
    pub state: GpioState,
    /// Monotonic timestamp in microseconds since firmware boot.
    pub timestamp_us: u64,
}

/// Request to subscribe a GPIO pin to edge-event monitoring.
///
/// Once subscribed, the pin is exclusively owned by the monitor task.
/// Regular GPIO operations ([`GpioGet`], [`GpioPut`], wait, set-config)
/// on this pin will return [`GpioError::PinMonitored`] until
/// [`GpioUnsubscribe`] is called.
#[derive(Serialize, Deserialize, Schema, Debug, PartialEq)]
pub struct GpioSubscribeRequest {
    /// GPIO pin index (0–3).
    pub pin: u8,
    /// Which edges to monitor.
    pub edge: GpioEdge,
}

/// Request to unsubscribe a GPIO pin from edge-event monitoring.
///
/// The pin is returned to normal GPIO mode and can be used for regular
/// operations again.
#[derive(Serialize, Deserialize, Schema, Debug, PartialEq)]
pub struct GpioUnsubscribeRequest {
    /// GPIO pin index (0–3).
    pub pin: u8,
}

// --- Set config

/// Request to reconfigure I2C bus parameters.
///
/// Takes effect immediately. The firmware applies the new frequency before
/// processing the next I2C operation.
#[derive(Serialize, Deserialize, Schema, Debug, PartialEq)]
pub struct I2cSetConfigurationRequest {
    /// I2C bus clock frequency.
    pub frequency: I2cFrequency,
}

// WARNING: do not reorder variants — postcard encodes by index, not discriminant.
/// I2C bus clock frequency.
///
/// The RP2350 supports Standard (100 kHz), Fast (400 kHz), and Fast+ (1 MHz)
/// modes. Ultra-Fast mode is defined by the specification but not supported by
/// the RP2350 hardware.
#[derive(Serialize, Deserialize, Schema, Debug, Clone, Copy, PartialEq, Eq)]
#[repr(u8)]
pub enum I2cFrequency {
    /// Standard mode — 100 kHz.
    Standard = 0,
    /// Fast mode — 400 kHz.
    Fast = 1,
    /// Fast+ mode — 1 MHz.
    FastPlus = 2,
}

/// Error returned when I2C configuration fails.
///
/// This is a convenience alias — I2C configuration shares the same error
/// type as other I2C operations.
pub type I2cConfigError = I2cError;

/// Request to reconfigure SPI bus parameters.
///
/// Takes effect immediately. The firmware applies the new settings before
/// processing the next SPI operation.
#[derive(Serialize, Deserialize, Schema, Debug, PartialEq)]
pub struct SpiSetConfigurationRequest {
    /// SPI bus clock frequency in Hz.
    pub spi_frequency: u32,
    /// SPI clock phase.
    pub spi_phase: SpiPhase,
    /// SPI clock polarity.
    pub spi_polarity: SpiPolarity,
}

/// SPI clock phase setting.
//
// WARNING: Do not reorder enum variants — postcard serializes by
// variant index, not by discriminant. Reordering breaks wire compat.
#[derive(Serialize, Deserialize, Schema, Debug, Clone, Copy, PartialEq, Eq, Hash)]
pub enum SpiPhase {
    /// Data captured on the leading (first) clock edge.
    CaptureOnFirstTransition = 0,
    /// Data captured on the trailing (second) clock edge.
    CaptureOnSecondTransition = 1,
}

/// SPI clock polarity setting.
//
// WARNING: Do not reorder enum variants — postcard serializes by
// variant index, not by discriminant. Reordering breaks wire compat.
#[derive(Serialize, Deserialize, Schema, Debug, Clone, Copy, PartialEq, Eq, Hash)]
pub enum SpiPolarity {
    /// Clock idles at logic low (CPOL=0).
    IdleLow = 0,
    /// Clock idles at logic high (CPOL=1).
    IdleHigh = 1,
}

/// Error returned when SPI configuration fails.
///
/// This is a convenience alias — SPI configuration shares the same error
/// type as other SPI operations.
pub type SpiConfigError = SpiError;

// --- UART

// WARNING: Do not reorder enum variants - postcard serializes by
// variant index, not by discriminant. Reordering breaks wire compat.
/// UART word length, in data bits per character.
///
/// The RP2350's PL011 encodes this in `UARTLCR_H.WLEN`, which is two bits
/// wide, so 5..=8 is the complete hardware range and there is no 9-bit mode.
/// The discriminants below **are** the `WLEN` encoding, which the firmware
/// relies on; `uart_data_bits_discriminants_are_the_wlen_encoding` pins it.
#[derive(Serialize, Deserialize, Schema, Debug, Clone, Copy, PartialEq, Eq)]
#[repr(u8)]
pub enum UartDataBits {
    /// Five data bits.
    Five = 0,
    /// Six data bits.
    Six = 1,
    /// Seven data bits.
    Seven = 2,
    /// Eight data bits. The power-on default.
    Eight = 3,
}

// WARNING: Do not reorder enum variants - postcard serializes by
// variant index, not by discriminant. Reordering breaks wire compat.
/// UART parity mode.
///
/// `None`, `Odd` and `Even` use the PL011's `PEN`/`EPS` bits. `Mark` and
/// `Space` additionally set `SPS` (stick parity): with `SPS` set, `EPS = 0`
/// transmits and checks the parity bit as 1, and `EPS = 1` as 0.
///
/// Mark and space are unreachable through embassy's own `uart::Parity`, which
/// has only three variants. They are offered here because the firmware writes
/// the register directly.
///
/// These indices happen to coincide with Zephyr's `UART_CFG_PARITY_*`
/// ordinals. That is a **coincidence, not a contract**: nothing here is
/// derived from Zephyr's numbering and nothing constrains this enum to keep
/// tracking it. Consumers must map explicitly rather than casting, and no
/// test pins the correspondence, because pinning it would turn the
/// coincidence into a contract by accident.
#[derive(Serialize, Deserialize, Schema, Debug, Clone, Copy, PartialEq, Eq)]
#[repr(u8)]
pub enum UartParity {
    /// No parity bit. The power-on default.
    None = 0,
    /// Odd parity.
    Odd = 1,
    /// Even parity.
    Even = 2,
    /// Parity bit always 1.
    Mark = 3,
    /// Parity bit always 0.
    Space = 4,
}

// WARNING: Do not reorder enum variants - postcard serializes by
// variant index, not by discriminant. Reordering breaks wire compat.
/// UART stop-bit count.
///
/// The PL011 has a single `STP2` bit, so one and two stop bits are the
/// complete hardware range. Half stop bits are not representable.
///
/// These indices deliberately do **not** match Zephyr's
/// `uart_config_stop_bits` (`0_5 = 0, 1 = 1, 1_5 = 2, 2 = 3`). Matching it
/// would bake a foreign subsystem's ABI into this wire format and leave two
/// permanently unrepresentable holes; consumers map explicitly instead.
#[derive(Serialize, Deserialize, Schema, Debug, Clone, Copy, PartialEq, Eq)]
#[repr(u8)]
pub enum UartStopBits {
    /// One stop bit. The power-on default.
    One = 0,
    /// Two stop bits.
    Two = 1,
}

/// Error from UART operations, propagated from firmware.
///
/// # Wire Compatibility
///
/// Variants are serialized by **index**. Do **not** reorder or insert
/// variants in the middle — only append at the end.
#[derive(Serialize, Deserialize, Schema, Debug, Clone, Copy, PartialEq, Eq)]
pub enum UartError {
    /// Request exceeds the firmware buffer limit ([`MAX_TRANSFER_SIZE`]).
    BufferTooLong,
    /// UART receiver FIFO overrun — data arrived faster than the firmware
    /// could process it.
    Overrun,
    /// A break condition was detected on the UART RX line.
    Break,
    /// Parity mismatch between received data and configured parity setting.
    Parity,
    /// The received character did not have a valid stop bit.
    Framing,
    /// The requested baud rate is invalid (zero or unsupported by hardware).
    InvalidBaudRate,
    /// An unspecified error occurred in the firmware.
    Other,
    /// The peripheral is not available on this hardware revision.
    // WARNING: Do not reorder — postcard encodes by variant index.
    Unsupported,
}

impl core::fmt::Display for UartError {
    fn fmt(&self, f: &mut core::fmt::Formatter<'_>) -> core::fmt::Result {
        match self {
            Self::BufferTooLong => write!(f, "buffer exceeds firmware limit"),
            Self::Overrun => write!(f, "UART receiver overrun"),
            Self::Break => write!(f, "UART break condition"),
            Self::Parity => write!(f, "UART parity error"),
            Self::Framing => write!(f, "UART framing error"),
            Self::InvalidBaudRate => write!(f, "invalid baud rate"),
            Self::Other => write!(f, "UART error"),
            Self::Unsupported => write!(f, "UART not supported on this hardware"),
        }
    }
}

/// Request to read bytes from the UART bus.
///
/// The firmware reads up to `count` bytes from the UART receive buffer.
/// If no data is immediately available, the firmware waits up to
/// `timeout_ms` milliseconds for at least one byte. Returns whatever
/// bytes are available (1 to `count`), or an empty result on timeout.
#[derive(Serialize, Deserialize, Schema, Debug, PartialEq)]
pub struct UartReadRequest {
    /// Maximum number of bytes to read (max [`MAX_TRANSFER_SIZE`]).
    pub count: u16,
    /// Maximum time to wait for data, in milliseconds. Use `0` for a single
    /// non-blocking poll that returns only already-buffered data. Non-zero
    /// values above the firmware's 30-minute ceiling are clamped to it.
    pub timeout_ms: u32,
}

/// Request to write bytes to the UART bus.
#[derive(Serialize, Deserialize, Schema, Debug, PartialEq)]
pub struct UartWriteRequest<'a> {
    /// Bytes to write.
    pub contents: &'a [u8],
}

/// Request to reconfigure UART bus parameters.
///
/// Takes effect immediately. The firmware applies the new configuration
/// before processing the next UART operation.
///
/// All four parameters are applied together; there is no partial update. A
/// caller that wants to change only the baud rate must read the current
/// configuration with `uart/get-config` first and echo the framing fields
/// back.
///
/// The framing values are limited to what the RP2350 PL011 can produce. See
/// [`UartDataBits`], [`UartParity`] and [`UartStopBits`].
#[derive(Serialize, Deserialize, Schema, Debug, PartialEq)]
pub struct UartSetConfigurationRequest {
    /// UART baud rate in bits per second. Must be non-zero.
    pub baud_rate: u32,
    /// Word length in data bits.
    pub data_bits: UartDataBits,
    /// Parity mode.
    pub parity: UartParity,
    /// Stop-bit count.
    pub stop_bits: UartStopBits,
}

/// Error returned when UART configuration fails.
///
/// This is a convenience alias — UART configuration shares the same error
/// type as other UART operations.
pub type UartConfigError = UartError;

/// Current UART bus configuration as reported by the firmware.
///
/// Returned by `uart/get-config`. Reflects the last successfully applied
/// configuration.
///
/// This is a software shadow of what was requested, not a register
/// read-back, so `baud_rate` is the value that was asked for rather than the
/// value the divisor actually achieves after rounding.
#[derive(Serialize, Deserialize, Schema, Debug, Clone, PartialEq, Eq)]
pub struct UartConfigurationInfo {
    /// UART baud rate in bits per second.
    pub baud_rate: u32,
    /// Word length in data bits.
    pub data_bits: UartDataBits,
    /// Parity mode.
    pub parity: UartParity,
    /// Stop-bit count.
    pub stop_bits: UartStopBits,
}

/// Current SPI bus configuration as reported by the firmware.
///
/// Returned by `spi/get-config`. The field names mirror
/// [`SpiSetConfigurationRequest`] for consistency.
#[derive(Serialize, Deserialize, Schema, Debug, Clone, PartialEq, Eq)]
pub struct SpiConfigurationInfo {
    /// SPI bus clock frequency in Hz.
    pub spi_frequency: u32,
    /// SPI clock phase.
    pub spi_phase: SpiPhase,
    /// SPI clock polarity.
    pub spi_polarity: SpiPolarity,
}

// --- PWM

/// Number of PWM output channels exposed by the firmware.
///
/// Channels 0–3 map to physical pins GPIO12–GPIO15 on the Pico 2 header.
/// Channels 0–1 share PWM slice 6; channels 2–3 share PWM slice 7.
pub const NUM_PWM_CHANNELS: usize = 4;

/// Error from PWM operations, propagated from firmware.
///
/// # Wire Compatibility
///
/// Variants are serialized by **index**. Do **not** reorder or insert
/// variants in the middle — only append at the end.
#[derive(Serialize, Deserialize, Schema, Debug, Clone, Copy, PartialEq, Eq)]
pub enum PwmError {
    /// The requested channel index exceeds the available PWM channels
    /// ([`NUM_PWM_CHANNELS`]).
    InvalidChannel,
    /// The requested duty cycle exceeds the maximum for the current
    /// configuration (i.e., `duty > top`).
    InvalidDutyCycle,
    /// The requested configuration is invalid (e.g., zero frequency or
    /// unsupported divider value).
    InvalidConfiguration,
    /// An unspecified error occurred in the firmware.
    Other,
}

impl core::fmt::Display for PwmError {
    fn fmt(&self, f: &mut core::fmt::Formatter<'_>) -> core::fmt::Result {
        match self {
            Self::InvalidChannel => write!(f, "invalid PWM channel"),
            Self::InvalidDutyCycle => write!(f, "duty cycle exceeds maximum"),
            Self::InvalidConfiguration => write!(f, "invalid PWM configuration"),
            Self::Other => write!(f, "PWM error"),
        }
    }
}

/// Request to set the duty cycle of a PWM channel.
///
/// The `duty` value is a raw compare value (0 to `top`). Use
/// [`PwmGetDutyCycle`] to query the current `max_duty` (top) before
/// computing a duty cycle from a percentage.
#[derive(Serialize, Deserialize, Schema, Debug, PartialEq)]
pub struct PwmSetDutyCycleRequest {
    /// PWM channel index (0–3).
    pub channel: u8,
    /// Raw duty cycle value (0 to top).
    pub duty: u16,
}

/// Request to query the current duty cycle of a PWM channel.
#[derive(Serialize, Deserialize, Schema, Debug, PartialEq)]
pub struct PwmGetDutyCycleRequest {
    /// PWM channel index (0–3).
    pub channel: u8,
}

/// Information about a PWM channel's current duty cycle.
///
/// The `max_duty` field corresponds to the slice's `top` register value.
/// The `current_duty` field is the raw compare value for the channel.
#[derive(Serialize, Deserialize, Schema, Debug, Clone, PartialEq, Eq)]
pub struct PwmDutyCycleInfo {
    /// Maximum duty cycle value (the `top` value of the PWM slice).
    pub max_duty: u16,
    /// Current duty cycle value (raw compare register).
    pub current_duty: u16,
}

/// Request to enable a PWM channel's slice.
///
/// **Note:** Channels 0–1 share a slice and channels 2–3 share a slice.
/// Enabling one channel enables the entire slice (both channels).
#[derive(Serialize, Deserialize, Schema, Debug, PartialEq)]
pub struct PwmEnableRequest {
    /// PWM channel index (0–3). The parent slice is enabled.
    pub channel: u8,
}

/// Request to disable a PWM channel's slice.
///
/// **Note:** Channels 0–1 share a slice and channels 2–3 share a slice.
/// Disabling one channel disables the entire slice (both channels).
#[derive(Serialize, Deserialize, Schema, Debug, PartialEq)]
pub struct PwmDisableRequest {
    /// PWM channel index (0–3). The parent slice is disabled.
    pub channel: u8,
}

/// Request to reconfigure the PWM slice behind a channel.
///
/// Sets the output frequency and phase-correct mode. The firmware
/// computes `top` and `divider` from the requested `frequency_hz`.
///
/// **Note:** Channels 0–1 share a slice and channels 2–3 share a slice.
/// Configuring one channel reconfigures the entire slice.
#[derive(Serialize, Deserialize, Schema, Debug, PartialEq)]
pub struct PwmSetConfigurationRequest {
    /// PWM channel index (0–3). Identifies the target slice.
    pub channel: u8,
    /// Desired PWM output frequency in Hz.
    pub frequency_hz: u32,
    /// Enable phase-correct mode. When `true`, the output frequency is
    /// halved and the pulse is centered.
    pub phase_correct: bool,
}

/// Request to query the current configuration of a PWM channel's slice.
#[derive(Serialize, Deserialize, Schema, Debug, PartialEq)]
pub struct PwmGetConfigurationRequest {
    /// PWM channel index (0–3).
    pub channel: u8,
}

/// Error returned when PWM configuration fails.
///
/// This is a convenience alias — PWM configuration shares the same error
/// type as other PWM operations.
pub type PwmConfigError = PwmError;

/// Current PWM slice configuration as reported by the firmware.
///
/// Returned by `pwm/get-config`. Reflects the last successfully applied
/// configuration.
#[derive(Serialize, Deserialize, Schema, Debug, Clone, PartialEq, Eq)]
pub struct PwmConfigurationInfo {
    /// Actual PWM output frequency in Hz (may differ slightly from
    /// the requested value due to divider/top quantization).
    pub frequency_hz: u32,
    /// Whether phase-correct mode is active.
    pub phase_correct: bool,
    /// Whether the slice is currently enabled.
    pub enabled: bool,
}

// --- ADC (Analog-to-Digital Converter)

/// Number of external (GPIO-based) ADC channels exposed by the firmware.
///
/// Channels [`AdcChannel::Adc0`] through [`AdcChannel::Adc3`] map to physical
/// pins GPIO26–GPIO29 on the Pico 2 header.
pub const NUM_ADC_GPIO_CHANNELS: usize = 4;

/// ADC resolution in bits.
///
/// The RP2350 has a 12-bit SAR ADC; raw readings are in the range 0–4095.
pub const ADC_RESOLUTION_BITS: u8 = 12;

/// Nominal ADC reference voltage in millivolts.
///
/// On RP2350, ADC readings are referenced to ADC_AVDD (nominally 3.3 V).
/// This is **not** a precision reference — actual voltage may vary with
/// supply quality.
pub const ADC_NOMINAL_REFERENCE_MV: u16 = 3300;

/// ADC channel selector.
///
/// Identifies which ADC input to sample. GPIO-based channels (`Adc0`–`Adc3`)
/// read external analog voltages on GPIO26–GPIO29.
///
/// # Wire Compatibility
///
/// Variants are serialized as discriminant integers (0–3). **Do not**
/// reorder or insert variants before existing ones — that changes the
/// wire encoding and breaks backward compatibility.
#[derive(Serialize, Deserialize, Schema, Debug, Clone, Copy, PartialEq, Eq)]
pub enum AdcChannel {
    /// ADC channel 0 — GPIO26.
    Adc0 = 0,
    /// ADC channel 1 — GPIO27.
    Adc1 = 1,
    /// ADC channel 2 — GPIO28.
    Adc2 = 2,
    /// ADC channel 3 — GPIO29.
    Adc3 = 3,
}

impl core::fmt::Display for AdcChannel {
    fn fmt(&self, f: &mut core::fmt::Formatter<'_>) -> core::fmt::Result {
        match self {
            Self::Adc0 => write!(f, "ADC0 (GPIO26)"),
            Self::Adc1 => write!(f, "ADC1 (GPIO27)"),
            Self::Adc2 => write!(f, "ADC2 (GPIO28)"),
            Self::Adc3 => write!(f, "ADC3 (GPIO29)"),
        }
    }
}

/// Error from ADC operations, propagated from firmware.
///
/// # Wire Compatibility
///
/// Variants are serialized as discriminant integers. **Do not** reorder or
/// insert variants before existing ones — that changes the wire encoding
/// and breaks backward compatibility.
#[derive(Serialize, Deserialize, Schema, Debug, Clone, Copy, PartialEq, Eq)]
pub enum AdcError {
    /// The ADC hardware signaled a conversion error.
    ConversionFailed,
    /// Catch-all for unexpected ADC errors.
    Other,
    /// The peripheral is not available on this hardware revision.
    // WARNING: Do not reorder — postcard encodes by variant index.
    Unsupported,
}

impl core::fmt::Display for AdcError {
    fn fmt(&self, f: &mut core::fmt::Formatter<'_>) -> core::fmt::Result {
        match self {
            Self::ConversionFailed => write!(f, "ADC conversion failed"),
            Self::Other => write!(f, "ADC error"),
            Self::Unsupported => write!(f, "ADC not supported on this hardware"),
        }
    }
}

/// Error returned when ADC configuration fails.
///
/// This is a convenience alias — ADC configuration shares the same error
/// type as other ADC operations.
pub type AdcConfigError = AdcError;

/// Request to perform a single-shot ADC read on a specific channel.
///
/// Returns a raw 12-bit value (0–4095). The host can convert to voltage
/// using `V = raw * nominal_reference_mv / 4096`.
#[derive(Serialize, Deserialize, Schema, Debug, PartialEq)]
pub struct AdcReadRequest {
    /// Which ADC channel to sample.
    pub channel: AdcChannel,
}

/// Current ADC configuration as reported by the firmware.
///
/// Returned by `adc/get-config`. Values are fixed for the RP2350 ADC
/// but exposed for host discovery and consistency with other peripherals.
#[derive(Serialize, Deserialize, Schema, Debug, Clone, PartialEq, Eq)]
pub struct AdcConfigurationInfo {
    /// ADC resolution in bits (always 12 for RP2350).
    pub resolution_bits: u8,
    /// Nominal ADC reference voltage in millivolts (typically 3300).
    ///
    /// **Note:** This is the nominal ADC_AVDD voltage, not a precision
    /// reference. Actual voltage may vary.
    pub nominal_reference_mv: u16,
    /// Number of external (GPIO-based) ADC channels.
    pub num_gpio_channels: u8,
}

// --- 1-Wire

/// Error from 1-Wire operations, propagated from firmware.
///
/// # Wire Compatibility
///
/// Variants are serialized by **index** (0, 1, 2, …). Do **not** reorder,
/// rename, or remove existing variants — only append new ones at the end.
#[derive(Serialize, Deserialize, Schema, Debug, Clone, Copy, PartialEq, Eq)]
pub enum OneWireError {
    /// No device responded to reset (no presence pulse detected).
    NoPresence,
    /// Bus communication error (short circuit, stuck bus, etc.).
    BusError,
    /// Requested transfer exceeds [`MAX_TRANSFER_SIZE`].
    BufferTooLong,
    /// Catch-all for unexpected 1-Wire errors.
    Other,
    /// The peripheral is not available on this hardware revision.
    // WARNING: Do not reorder — postcard encodes by variant index.
    Unsupported,
}

impl core::fmt::Display for OneWireError {
    fn fmt(&self, f: &mut core::fmt::Formatter<'_>) -> core::fmt::Result {
        match self {
            Self::NoPresence => write!(f, "no device present on 1-Wire bus"),
            Self::BusError => write!(f, "1-Wire bus error"),
            Self::BufferTooLong => write!(f, "buffer exceeds firmware limit"),
            Self::Other => write!(f, "1-Wire error"),
            Self::Unsupported => write!(f, "1-Wire not supported on this hardware"),
        }
    }
}

/// Request to read bytes from the 1-Wire bus.
///
/// The firmware reads `len` bytes from the bus after the host has already
/// issued the appropriate ROM and function commands via [`OneWireWrite`].
#[derive(Serialize, Deserialize, Schema, Debug, PartialEq)]
pub struct OneWireReadRequest {
    /// Number of bytes to read (max [`MAX_TRANSFER_SIZE`]).
    pub len: u16,
}

/// Request to write bytes to the 1-Wire bus.
///
/// Writes raw bytes (ROM commands, function commands, data) to the bus.
/// The host is responsible for issuing the correct 1-Wire command
/// sequences (e.g., Skip ROM `0xCC` + Convert T `0x44`).
#[derive(Serialize, Deserialize, Schema, Debug, PartialEq)]
pub struct OneWireWriteRequest<'a> {
    /// Bytes to write to the bus.
    pub data: &'a [u8],
}

/// Request to write bytes to the 1-Wire bus with strong pullup.
///
/// After writing, the firmware drives the data line high for
/// `pullup_duration_ms` milliseconds to supply parasitic power.
/// This is required for devices like DS18B20 that draw power from
/// the data line during temperature conversion.
#[derive(Serialize, Deserialize, Schema, Debug, PartialEq)]
pub struct OneWireWritePullupRequest<'a> {
    /// Bytes to write to the bus.
    pub data: &'a [u8],
    /// Duration in milliseconds to hold the strong pullup after writing.
    pub pullup_duration_ms: u16,
}

// --- Transaction Batching
///
/// This limits stack usage on the firmware side. Each operation requires
/// a small amount of bookkeeping during execution.
pub const MAX_BATCH_OPS: usize = 64;

/// A single I2C operation for building a batch request.
///
/// The typed ops are serialized by postcard into the `ops` byte stream
/// of [`I2cBatchRequest`]. Use [`encode_i2c_batch_ops`] on the host
/// side to produce it, and [`postcard::take_from_bytes`] on the firmware
/// side to iterate.
///
/// WARNING: do not reorder variants — postcard encodes by index, not discriminant.
#[derive(Serialize, Deserialize, Schema, Debug, Clone, PartialEq)]
pub enum I2cBatchOp<'a> {
    /// Read `len` bytes from the device.
    Read { len: u16 },
    /// Write `data` to the device.
    Write {
        #[serde(borrow)]
        data: &'a [u8],
    },
}

/// A single SPI operation for building a batch request.
///
/// The typed ops are serialized by postcard into the `ops` byte stream
/// of [`SpiBatchRequest`]. Use [`encode_spi_batch_ops`] on the host
/// side to produce it, and [`postcard::take_from_bytes`] on the firmware
/// side to iterate.
///
/// WARNING: do not reorder variants — postcard encodes by index, not discriminant.
#[derive(Serialize, Deserialize, Schema, Debug, Clone, PartialEq)]
pub enum SpiBatchOp<'a> {
    /// Read `len` bytes from the bus (MISO only).
    Read { len: u16 },
    /// Write `data` to the bus (MOSI only).
    Write {
        #[serde(borrow)]
        data: &'a [u8],
    },
    /// Full-duplex transfer: send `data` on MOSI, receive same number of bytes on MISO.
    Transfer {
        #[serde(borrow)]
        data: &'a [u8],
    },
    /// Delay for `ns` nanoseconds (best-effort, firmware resolution).
    DelayNs { ns: u32 },
}

/// Request to execute a batch of I2C operations as a single transaction.
///
/// The `ops` field contains a sequence of postcard-serialized
/// [`I2cBatchOp`] values. Use [`encode_i2c_batch_ops`] on the host
/// side to build it from a typed slice.
///
/// ## Bus semantics
///
/// The whole batch executes as one I2C transaction, matching the
/// `embedded-hal` [`I2c::transaction`] contract:
///
/// - a START and address precede the first operation;
/// - adjacent operations of the same type are sent back to back with no
///   STOP and no repeated START between them, so two adjacent `Write`
///   ops form a single gather write;
/// - a direction change emits a repeated START and a re-addressing;
/// - a STOP follows the last operation, and only the last one.
///
/// Requires firmware built from schema 0.7 or newer. Older firmware
/// executes each operation as a separate transaction.
///
/// [`I2c::transaction`]: https://docs.rs/embedded-hal/1.0.0/embedded_hal/i2c/trait.I2c.html#tymethod.transaction
///
/// ## Response
///
/// On success, the response contains the concatenated read data from all
/// Read operations in order. The host already knows the expected lengths
/// from the request, so it can split the response accordingly.
///
/// ## Limitations
///
/// - Total read data must not exceed [`MAX_RESPONSE_PAYLOAD`], which is far
///   tighter than [`MAX_TRANSFER_SIZE`]. A batch reading more than a single
///   response frame can carry would otherwise execute in full — including
///   every `Write` — and only then lose its reply (issue #179).
/// - The whole request frame, header and encoding overhead included, must
///   not exceed [`MAX_REQUEST_FRAME`]. This is the only bound on a batch's
///   outgoing bytes, and it bounds the aggregate rather than any one
///   operation. A longer frame is discarded by the firmware's receiver
///   before any handler runs, so it would otherwise produce no reply at all
///   (issue #186). Size a batch with [`i2c_batch_request_frame_len`].
/// - Maximum [`MAX_BATCH_OPS`] operations per batch
#[derive(Serialize, Deserialize, Schema, Debug, PartialEq)]
pub struct I2cBatchRequest<'a> {
    /// 7-bit I2C slave address.
    pub address: u8,
    /// Number of operations encoded in `ops`.
    pub count: u16,
    /// Postcard-serialized [`I2cBatchOp`] sequence.
    pub ops: &'a [u8],
}

/// Error returned when an I2C batch transaction fails.
///
/// ## Interpreting `failed_op`
///
/// The batch executes as one atomic transaction, so the two error
/// classes attribute differently:
///
/// - **Validation** errors are raised before any bus access and carry the
///   exact zero-based index of the offending operation.
/// - **Bus** errors are reported by the transaction as a whole and cannot
///   be attributed to one operation. They always carry `failed_op = 0`.
///
/// A non-zero `failed_op` therefore always means validation. A zero
/// `failed_op` means either the first operation failed validation or the
/// transaction failed on the bus; `kind` distinguishes them.
///
/// No read data is returned on failure.
#[derive(Serialize, Deserialize, Schema, Debug, Clone, Copy, PartialEq, Eq)]
pub struct I2cBatchError {
    /// Zero-based index of the operation that failed.
    pub failed_op: u16,
    /// The I2C error that occurred.
    pub kind: I2cError,
}

impl core::fmt::Display for I2cBatchError {
    fn fmt(&self, f: &mut core::fmt::Formatter<'_>) -> core::fmt::Result {
        write!(
            f,
            "I2C batch operation {} failed: {}",
            self.failed_op, self.kind
        )
    }
}

/// Request to execute a batch of SPI operations as a single transaction.
///
/// The firmware asserts CS on the specified pin before executing the
/// operations, and deasserts CS after completion — including when an
/// operation fails after CS was asserted. Failures raised *before* CS is
/// driven (pin validation and refusals) leave the pin untouched; see
/// [`SpiBatchRequest::cs_pin`] for the full contract. This provides atomic
/// [`SpiDevice::transaction`] semantics.
///
/// The `ops` field contains a sequence of postcard-serialized
/// [`SpiBatchOp`] values. Use [`encode_spi_batch_ops`] on the host
/// side to build it from a typed slice.
///
/// ## Response
///
/// On success, the response contains concatenated data from Read and
/// Transfer operations in order. The host knows expected lengths from
/// the request.
///
/// [`SpiDevice::transaction`]: embedded_hal::spi::SpiDevice::transaction
#[derive(Serialize, Deserialize, Schema, Debug, PartialEq)]
pub struct SpiBatchRequest<'a> {
    /// GPIO pin index to use as chip select.
    ///
    /// Firmware implementing this protocol revision drives the pin as an output
    /// during a successful batch and leaves it configured as an output,
    /// deasserted high; the prior direction is not restored. An execution failure
    /// after assertion also leaves CS deasserted high. Pre-validation and refusal
    /// failures leave the pin untouched. Pins explicitly configured as inputs are
    /// refused; firmware predating this contract may instead reconfigure them.
    pub cs_pin: u8,
    /// Number of operations encoded in `ops`.
    pub count: u16,
    /// Postcard-serialized [`SpiBatchOp`] sequence.
    pub ops: &'a [u8],
}

/// Error returned when an SPI batch transaction fails.
///
/// See [`I2cBatchError`] for the general pattern. For SPI batches, the
/// firmware deasserts CS before returning whenever it had already asserted
/// it; errors raised before CS is driven leave the pin untouched. See
/// [`SpiBatchRequest::cs_pin`] for the full contract.
#[derive(Serialize, Deserialize, Schema, Debug, Clone, Copy, PartialEq, Eq)]
pub struct SpiBatchError {
    /// Zero-based index of the operation that failed.
    pub failed_op: u16,
    /// The SPI error that occurred.
    pub kind: SpiError,
}

impl core::fmt::Display for SpiBatchError {
    fn fmt(&self, f: &mut core::fmt::Formatter<'_>) -> core::fmt::Result {
        write!(
            f,
            "SPI batch operation {} failed: {}",
            self.failed_op, self.kind
        )
    }
}

/// Encode a sequence of I2C batch operations into the postcard wire format.
///
/// Returns the serialized byte stream suitable for [`I2cBatchRequest::ops`].
///
/// There is no limit on the size of an individual operation: each one is
/// serialized straight into the growable output buffer, and unlike a plain
/// write it is not bounded by [`MAX_TRANSFER_SIZE`], because the firmware
/// streams it out of the received frame rather than through its scratch
/// buffer.
///
/// The *total* request is bounded, by [`MAX_REQUEST_FRAME`]. This function
/// still does not police that — it has no view of the header — but
/// [`i2c_batch_request_frame_len`] and [`spi_batch_request_frame_len`] do,
/// and `pico-de-gallo-lib` applies them before transmission (issue #186).
///
/// # Panics
///
/// Panics if `ops.len()` exceeds [`MAX_BATCH_OPS`]. Serialization itself
/// cannot fail, because [`postcard::to_extend`] only reports an error when the
/// sink rejects a write and [`Vec`] never does.
#[cfg(feature = "use-std")]
pub fn encode_i2c_batch_ops(ops: &[I2cBatchOp<'_>]) -> Vec<u8> {
    assert!(ops.len() <= MAX_BATCH_OPS, "too many batch operations");
    let mut buf = Vec::new();
    for op in ops {
        buf = postcard::to_extend(op, buf).expect("serializing into a Vec cannot fail");
    }
    buf
}

/// Encode a sequence of SPI batch operations into the postcard wire format.
///
/// Returns the serialized byte stream suitable for [`SpiBatchRequest::ops`].
///
/// There is no limit on the size of an individual operation: each one is
/// serialized straight into the growable output buffer, and unlike a plain
/// write it is not bounded by [`MAX_TRANSFER_SIZE`], because the firmware
/// streams it out of the received frame rather than through its scratch
/// buffer.
///
/// The *total* request is bounded, by [`MAX_REQUEST_FRAME`]. This function
/// still does not police that — it has no view of the header — but
/// [`i2c_batch_request_frame_len`] and [`spi_batch_request_frame_len`] do,
/// and `pico-de-gallo-lib` applies them before transmission (issue #186).
///
/// # Panics
///
/// Panics if `ops.len()` exceeds [`MAX_BATCH_OPS`]. Serialization itself
/// cannot fail, because [`postcard::to_extend`] only reports an error when the
/// sink rejects a write and [`Vec`] never does.
#[cfg(feature = "use-std")]
pub fn encode_spi_batch_ops(ops: &[SpiBatchOp<'_>]) -> Vec<u8> {
    assert!(ops.len() <= MAX_BATCH_OPS, "too many batch operations");
    let mut buf = Vec::new();
    for op in ops {
        buf = postcard::to_extend(op, buf).expect("serializing into a Vec cannot fail");
    }
    buf
}

/// Compute the total number of bytes that will appear in the response for
/// an I2C batch — the sum of all Read lengths.
pub fn i2c_batch_response_len(ops: &[I2cBatchOp<'_>]) -> usize {
    ops.iter()
        .map(|op| match op {
            I2cBatchOp::Read { len } => *len as usize,
            I2cBatchOp::Write { .. } => 0,
        })
        .sum()
}

/// Compute the total number of bytes that will appear in the response for
/// an SPI batch — the sum of Read and Transfer lengths.
pub fn spi_batch_response_len(ops: &[SpiBatchOp<'_>]) -> usize {
    ops.iter()
        .map(|op| match op {
            SpiBatchOp::Read { len } => *len as usize,
            SpiBatchOp::Transfer { data } => data.len(),
            _ => 0,
        })
        .sum()
}

/// Encoded length of `n` as a postcard varint, in bytes.
///
/// postcard writes an unsigned integer as LEB128: seven payload bits per
/// byte, high bit set on every byte but the last. Used to size the
/// `count` field and the two length prefixes that a batch request carries,
/// none of which are a fixed width.
const fn varint_len(mut n: usize) -> usize {
    let mut len = 1;
    while n >= 0x80 {
        n >>= 7;
        len += 1;
    }
    len
}

/// Encoded length of one [`I2cBatchOp`] in the `ops` byte stream.
///
/// One byte of variant index — both variants are below `0x80`, so the index
/// varint is always one byte — then the operation's own fields.
fn i2c_batch_op_len(op: &I2cBatchOp<'_>) -> usize {
    1 + match op {
        I2cBatchOp::Read { len } => varint_len(*len as usize),
        I2cBatchOp::Write { data } => varint_len(data.len()) + data.len(),
    }
}

/// Encoded length of one [`SpiBatchOp`] in the `ops` byte stream.
fn spi_batch_op_len(op: &SpiBatchOp<'_>) -> usize {
    1 + match op {
        SpiBatchOp::Read { len } => varint_len(*len as usize),
        SpiBatchOp::Write { data } | SpiBatchOp::Transfer { data } => {
            varint_len(data.len()) + data.len()
        }
        SpiBatchOp::DelayNs { ns } => varint_len(*ns as usize),
    }
}

/// Bytes a batch request occupies around its encoded operation stream.
///
/// The shared shape of [`I2cBatchRequest`] and [`SpiBatchRequest`]: a `u8`
/// selector (`address` or `cs_pin`, one plain byte — postcard does not
/// varint a `u8`), the `u16` operation `count`, and the `ops` slice's own
/// varint length prefix.
fn batch_request_frame_len(count: usize, encoded_ops_len: usize) -> usize {
    REQUEST_HEADER_LEN_MAX + 1 + varint_len(count) + varint_len(encoded_ops_len) + encoded_ops_len
}

/// Compute the number of bytes an I2C batch occupies as a request frame on
/// the wire, header included.
///
/// The mirror of [`i2c_batch_response_len`], and the quantity to compare
/// against [`MAX_REQUEST_FRAME`]. A batch is the only supported way to
/// build an over-ceiling request, because its aggregate outgoing bytes are
/// bounded by nothing else (issue #186).
///
/// Assumes the widest header, so the answer does not depend on whether the
/// caller's client has received a reply yet — see [`REQUEST_HEADER_LEN_MAX`].
/// On a warm connection the real frame is six bytes shorter than this.
///
/// Computed rather than measured so it costs no second encoding pass; the
/// arithmetic is pinned against [`encode_i2c_batch_ops`] and against
/// [`postcard::to_allocvec`] of a real [`I2cBatchRequest`] by
/// `i2c_batch_request_frame_len_matches_a_real_encoding`.
pub fn i2c_batch_request_frame_len(ops: &[I2cBatchOp<'_>]) -> usize {
    let encoded: usize = ops.iter().map(i2c_batch_op_len).sum();
    batch_request_frame_len(ops.len(), encoded)
}

/// Compute the number of bytes an SPI batch occupies as a request frame on
/// the wire, header included.
///
/// The send-direction counterpart of [`spi_batch_response_len`]. `Write`
/// and `Transfer` payloads both travel out; `Read` and `DelayNs` cost only
/// their operation encoding. See [`i2c_batch_request_frame_len`] for why
/// the widest header is assumed.
pub fn spi_batch_request_frame_len(ops: &[SpiBatchOp<'_>]) -> usize {
    let encoded: usize = ops.iter().map(spi_batch_op_len).sum();
    batch_request_frame_len(ops.len(), encoded)
}

// --- Version
/// Firmware version information.
#[derive(Serialize, Deserialize, Schema, Debug, PartialEq)]
pub struct VersionInfo {
    /// Major version number.
    pub major: u16,
    /// Minor version number.
    pub minor: u16,
    /// Patch version number.
    pub patch: u32,
}

// --- Device Info

/// Hardware capabilities — a bitflag set describing which peripherals are
/// available on the connected device.
///
/// Each capability is a single bit. New capabilities can be added by
/// defining new constants without changing the wire format — existing
/// bits remain stable.
///
/// Use [`BitOr`](core::ops::BitOr) to combine flags and
/// [`contains`](Capabilities::contains) to test them:
///
/// ```
/// use pico_de_gallo_internal::Capabilities;
///
/// let caps = Capabilities::I2C | Capabilities::SPI;
/// assert!(caps.contains(Capabilities::I2C));
/// assert!(!caps.contains(Capabilities::UART));
/// ```
#[derive(Serialize, Deserialize, Schema, Debug, PartialEq, Eq, Clone, Copy)]
pub struct Capabilities(pub u64);

impl Capabilities {
    /// No capabilities.
    pub const NONE: Self = Self(0);
    /// I2C bus support (bit 0).
    pub const I2C: Self = Self(1 << 0);
    /// SPI bus support (bit 1).
    pub const SPI: Self = Self(1 << 1);
    /// UART support (bit 2).
    pub const UART: Self = Self(1 << 2);
    /// GPIO support (bit 3).
    pub const GPIO: Self = Self(1 << 3);
    /// PWM output support (bit 4).
    pub const PWM: Self = Self(1 << 4);
    /// ADC input support (bit 5).
    pub const ADC: Self = Self(1 << 5);
    /// 1-Wire bus support (bit 6).
    pub const ONEWIRE: Self = Self(1 << 6);

    /// Returns `true` if all bits in `other` are set in `self`.
    pub const fn contains(self, other: Self) -> bool {
        (self.0 & other.0) == other.0
    }

    /// Returns the raw `u64` bitfield value.
    pub const fn bits(self) -> u64 {
        self.0
    }
}

impl core::ops::BitOr for Capabilities {
    type Output = Self;

    fn bitor(self, rhs: Self) -> Self {
        Self(self.0 | rhs.0)
    }
}

impl core::ops::BitAnd for Capabilities {
    type Output = Self;

    fn bitand(self, rhs: Self) -> Self {
        Self(self.0 & rhs.0)
    }
}

/// Maximum length of [`DeviceInfo::build_id()`], in bytes.
///
/// The field must always be spelled `heapless::String<BUILD_ID_CAPACITY>`,
/// leaving `LenT` at its default. `postcard-schema` implements `Schema` only
/// for `String<N>` at the default `LenT`, so naming a non-default `LenT`
/// silently breaks the `Schema` derive.
///
/// This is a *receive-side* bound. `heapless` deserialization rejects a longer
/// string rather than truncating it, so the firmware build script is
/// responsible for truncating; see `crates/pico-de-gallo-firmware/build.rs`.
/// Raising this value is not a wire-format change (the encoding is a plain
/// postcard string either way), but it is a `Schema` change and still needs a
/// lockstep bump per AGENTS.md §6.2.
pub const BUILD_ID_CAPACITY: usize = 64;

/// Extended device information including firmware version, schema version,
/// hardware version, and peripheral capabilities.
///
/// This is returned by a separate endpoint from [`VersionInfo`] so that
/// changes here cannot disturb the `version` endpoint. That separation is
/// what keeps `version` working against a peer whose `device/info` has
/// re-keyed: [`VersionInfo`]'s schema is unchanged, so the `version`
/// endpoint key is unchanged, and old and new peers still match each
/// other's frames. It is not that older hosts parse `DeviceInfo`
/// leniently — they never see it.
// CHANGING THIS TYPE IS QUALITATIVELY WORSE THAN CHANGING ANY OTHER WIRE
// TYPE. Think hard before adding, removing, or retyping a field here.
//
// postcard-rpc keys every endpoint by `Key::for_path::<T>(path)`, i.e. a
// hash of the type's `Schema` together with the path string, and the
// `endpoints!` macro derives `RESP_KEY` from the RESPONSE type's schema.
// Any change to a request or response type's shape therefore silently
// re-keys that endpoint, appends included. A peer built against the other
// shape replies under the other key; the receiving dispatcher finds no
// match, drops the frame, and never wakes the pending call. The call does
// not return. This is NOT a decode error -- postcard is never reached --
// so `map_validate_error` never sees a `DeserFailed`.
//
// For every other wire type that is survivable, because `device/info`
// itself still answers and `PicoDeGallo::validate()` reports the version
// difference as a `SchemaMismatch`. For THIS type it is not: re-keying
// `device/info` breaks the very probe that would have reported the
// mismatch, so the schema numbers that describe the incompatibility are
// sealed inside the one message that is dropped. `validate()` can only
// time out, indistinguishable from an unresponsive board, and bumping the
// schema version does not help -- the version is payload, not key.
//
// `DeviceInfo` is thus a blind spot for its own versioning mechanism. See
// `device_info_response_key_is_pinned` below, which fails the suite rather
// than letting a re-key reach the field silently.
#[derive(Serialize, Deserialize, Schema, Debug, PartialEq)]
pub struct DeviceInfo {
    /// Firmware version — major.
    pub fw_major: u16,
    /// Firmware version — minor.
    pub fw_minor: u16,
    /// Firmware version — patch.
    pub fw_patch: u32,
    /// Schema (wire protocol) version — major.
    pub schema_major: u16,
    /// Schema (wire protocol) version — minor.
    pub schema_minor: u16,
    /// Schema (wire protocol) version — patch.
    pub schema_patch: u32,
    /// Hardware revision number (1 = original Pico 2 board).
    pub hw_version: u8,
    /// Peripheral capabilities of the connected device.
    pub capabilities: Capabilities,
    /// Runtime-authoritative number of user-controllable GPIO pins.
    ///
    /// Valid GPIO and SPI chip-select indices are `0..num_gpios`; when this value
    /// is zero, no index is valid. This supersedes the compile-time [`NUM_GPIOS`]
    /// default and must never be synthesized or defaulted when `device/info`
    /// decoding fails.
    pub num_gpios: u8,
    /// Firmware build identity.
    ///
    /// The output of `git describe --always --dirty --tags --match
    /// firmware-v*` captured when the firmware was built, or `"unknown"` when
    /// git was unavailable at build time.
    ///
    /// Informational only. This is **never** a compatibility gate: schema
    /// version answers "can we talk?", and this field answers "are you the
    /// build I think you are?". `PicoDeGallo::validate()` deliberately ignores
    /// it. Use [`DeviceInfo::build_id()`] to read it as a `&str`.
    pub build_id: heapless::String<BUILD_ID_CAPACITY>,
}

impl DeviceInfo {
    /// The firmware build identity as a string slice.
    ///
    /// Provided so host crates never need to name `heapless` themselves.
    ///
    /// Note for doc authors: this method and the `build_id` field share a
    /// name, so a bare intra-doc link `[DeviceInfo::build_id]` is ambiguous
    /// and fails the `RUSTDOCFLAGS` doc job. Always write
    /// `[DeviceInfo::build_id()]` for this method.
    pub fn build_id(&self) -> &str {
        &self.build_id
    }
}
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
