OpenDevicePartnership/pico-de-gallo/crates/pico-de-gallo-app/src/lib.rs

//! Command-line interface for the Pico de Gallo USB bridge.
//!
//! The `gallo` CLI provides direct access to I2C, SPI, UART, GPIO, PWM, ADC, and 1-Wire peripherals
//! connected through a Pico de Gallo device. It is built with
//! [clap](https://docs.rs/clap) and supports:
//!
//! - **I2C**: bus scanning, read, write, and write-then-read operations
//! - **SPI**: read, write, full-duplex transfer, and write-then-read
//! - **UART**: read, write, flush, and baud rate configuration
//! - **PWM**: duty cycle control, enable/disable, frequency/phase configuration
//! - **ADC**: single-shot reads, configuration queries
//! - **1-Wire**: reset, read, write, strong-pullup write, ROM search
//! - **GPIO**: read/write pins, edge event monitoring with subscribe/unsubscribe
//! - **Configuration**: set I2C/SPI/UART bus frequencies and SPI mode
//! - **Device management**: list connected devices, query firmware version
//!
//! # Examples
//!
//! ```console
//! $ gallo list
//! $ gallo version
//! $ gallo i2c scan
//! $ gallo i2c read -a 0x48 -c 2
//! $ gallo i2c write -a 0x50 -b 0xDE 0xAD
//! $ gallo spi transfer -b 0x01 0x02 0x03
//! $ gallo set-config --i2c-frequency 400000 --spi-frequency 1000000
//! ```
//!
//! # Output Formats
//!
//! Read data can be displayed in three formats via the `-f` / `--format` flag:
//! - `hex` (default): hexadecimal byte dump
//! - `binary`: raw bytes written to stdout
//! - `ascii`: printable characters shown, non-printable replaced with `.`

use clap::{Parser, Subcommand, ValueEnum};
use color_eyre::{Result, eyre::eyre};
use pico_de_gallo_lib::{
    AdcChannel, DeviceInfo, GpioEdge, I2cFrequency, PicoDeGallo, SpiPhase, SpiPolarity, ValidateError, list_devices,
};
use pico_de_gallo_lib::{GpioDirection, GpioPull, GpioState};
use pico_de_gallo_lib::{UartDataBits, UartParity, UartStopBits};
use std::num::ParseIntError;
use std::time::Duration;
use tabled::builder::Builder;
use tabled::settings::object::Rows;
use tabled::settings::{Alignment, Style};

/// How long `gallo version` waits for `device/info` before falling back to
/// the legacy `version` endpoint.
///
/// Deliberately far shorter than `pico_de_gallo_lib::DEVICE_INFO_TIMEOUT`
/// (300 s). That bound is sized for the worst-case *firmware* occupancy:
/// `spi_batch` accepts up to 64 delay operations of `u32::MAX` nanoseconds
/// each, and postcard-rpc dispatches handlers serially, so any request can
/// legitimately queue behind minutes of user-requested delay. `device/info`
/// itself has no user-controllable work: it is a fixed-size response
/// assembled from constants.
///
/// `version` is a diagnostic command, and a diagnostic that hangs is worse
/// than useless. Five seconds is generous for USB enumeration plus one
/// round trip while still failing fast, and the fallback to the legacy
/// endpoint is strictly better than waiting: it is the path that keeps
/// working when the two sides were built from different trees.
const VERSION_DEVICE_INFO_TIMEOUT: Duration = Duration::from_secs(5);

/// I2C bus clock frequency for CLI argument parsing.
#[derive(ValueEnum, Clone, Copy, Debug, PartialEq, Eq)]
pub enum I2cFrequencyArg {
    /// Standard mode — 100 kHz
    Standard,
    /// Fast mode — 400 kHz
    Fast,
    /// Fast+ mode — 1 MHz
    FastPlus,
}

impl From<I2cFrequencyArg> for I2cFrequency {
    fn from(arg: I2cFrequencyArg) -> Self {
        match arg {
            I2cFrequencyArg::Standard => I2cFrequency::Standard,
            I2cFrequencyArg::Fast => I2cFrequency::Fast,
            I2cFrequencyArg::FastPlus => I2cFrequency::FastPlus,
        }
    }
}

/// GPIO pin direction for CLI argument parsing.
#[derive(ValueEnum, Clone, Copy, Debug, PartialEq, Eq)]
pub enum GpioDirectionArg {
    /// Configure pin as input
    Input,
    /// Configure pin as output
    Output,
}

impl From<GpioDirectionArg> for GpioDirection {
    fn from(arg: GpioDirectionArg) -> Self {
        match arg {
            GpioDirectionArg::Input => GpioDirection::Input,
            GpioDirectionArg::Output => GpioDirection::Output,
        }
    }
}

/// GPIO pull resistor configuration for CLI argument parsing.
#[derive(ValueEnum, Clone, Copy, Debug, PartialEq, Eq)]
pub enum GpioPullArg {
    /// No internal pull resistor
    None,
    /// Internal pull-up resistor
    Up,
    /// Internal pull-down resistor
    Down,
}
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
